jsyk/x65/doc/pic/aura-on-pcb.jpg

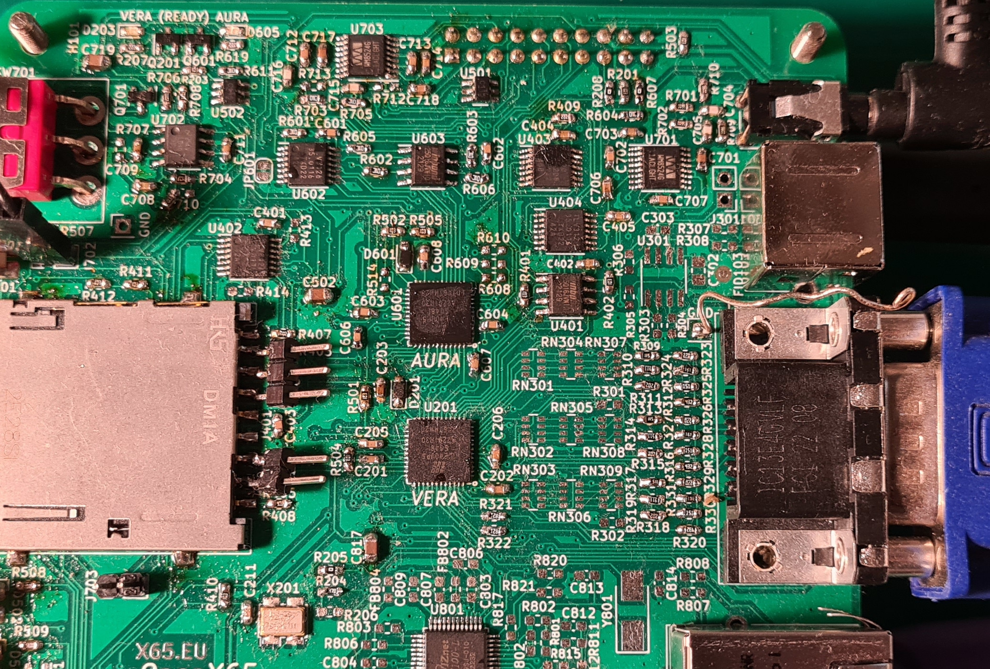
doc/pic/aura-on-pcb.jpg
