jsyk/x65/doc/pic/icd-random-trace-with-regread.png

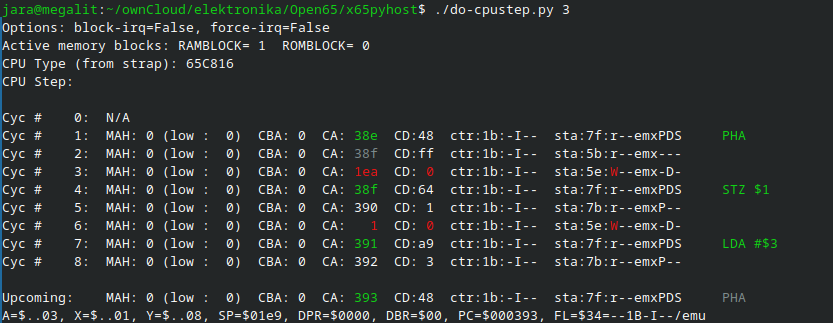
doc/pic/icd-random-trace-with-regread.png
