jsyk/x65/doc/pic/icd-regread-16bit-mx.png

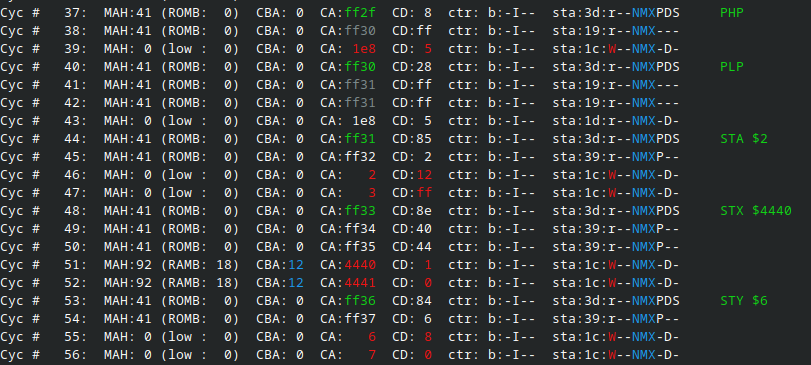
doc/pic/icd-regread-16bit-mx.png
