jsyk/x65/doc/pic/icd-regread-sta-stx-sty-bra.png

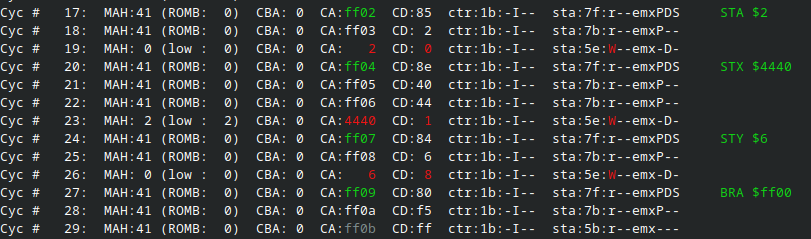
doc/pic/icd-regread-sta-stx-sty-bra.png
