jsyk/x65/doc/pic/of816-welcome.png

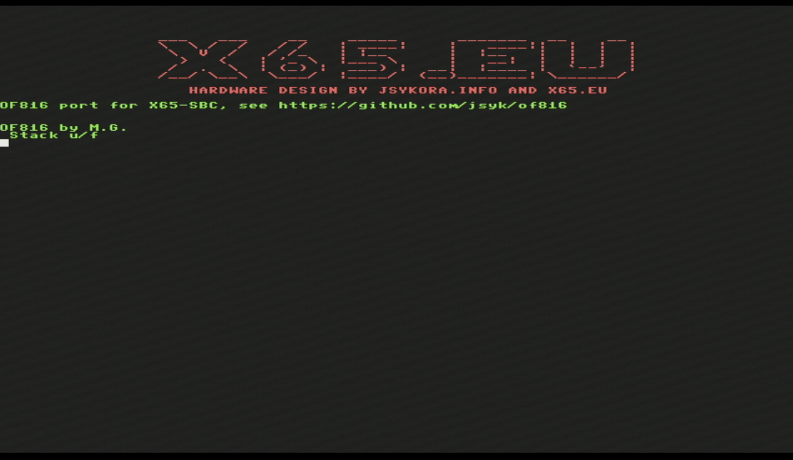
doc/pic/of816-welcome.png
