jsyk/x65/pcb/productions/2023-04-28--PCBWay-vabo-rev01/pcbdata2fab/Screenshot_20230428_151026.png

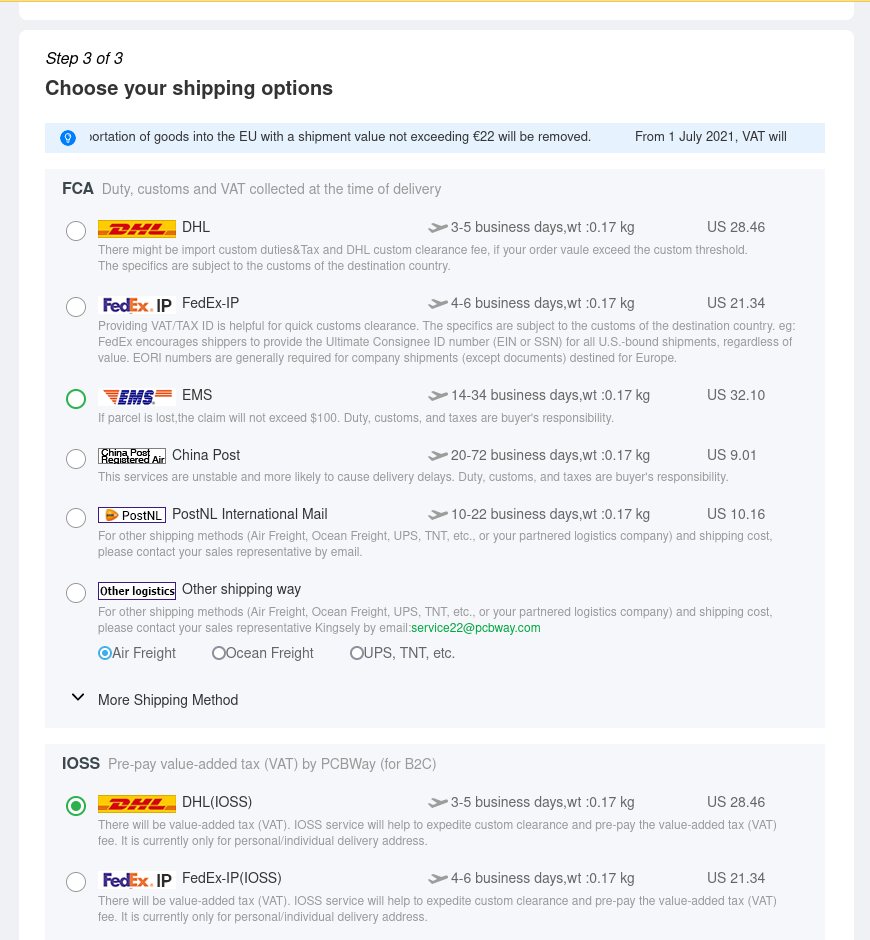
pcb/productions/2023-04-28--PCBWay-vabo-rev01/pcbdata2fab/Screenshot_20230428_151026.png
