jsyk/x65/pcb/productions/2024-01-14--JLCPCB-sbc-revA1/pcbdata2fab/Screenshot_20240114_134323.png

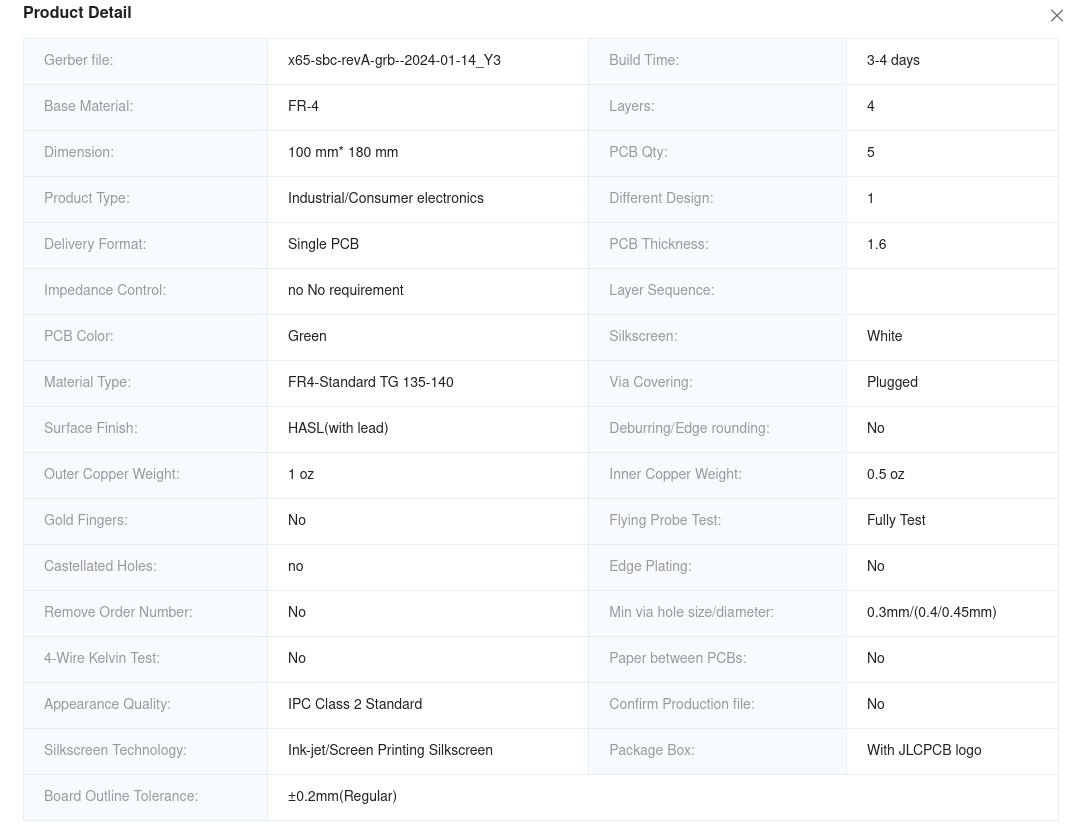
pcb/productions/2024-01-14--JLCPCB-sbc-revA1/pcbdata2fab/Screenshot_20240114_134323.png
