jsyk/x65/pcb/x65-sbc-revB1/pictures/1503_07_LUMBERG.jpg

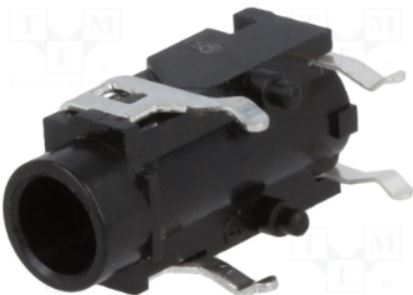
pcb/x65-sbc-revB1/pictures/1503_07_LUMBERG.jpg
