jsyk/x65/pcb/x65-sbc-revB1/pictures/DM1AA-SF-PEJ(82).jpg

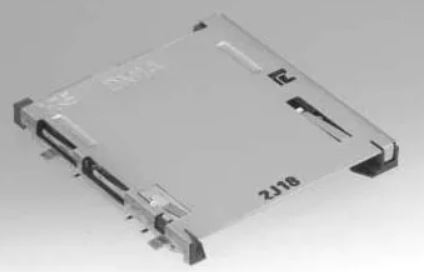
pcb/x65-sbc-revB1/pictures/DM1AA-SF-PEJ(82).jpg
