jsyk/x65/pcb/x65-sbc-revB1/pictures/DS1013-10RSIB-CONNFLY.jpg

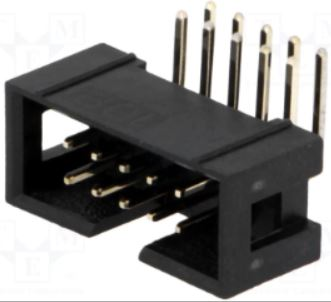
pcb/x65-sbc-revB1/pictures/DS1013-10RSIB-CONNFLY.jpg
