jsyk/x65/pcb/x65-sbc-revB1/pictures/ICD15S13E4GV00LF.jpg

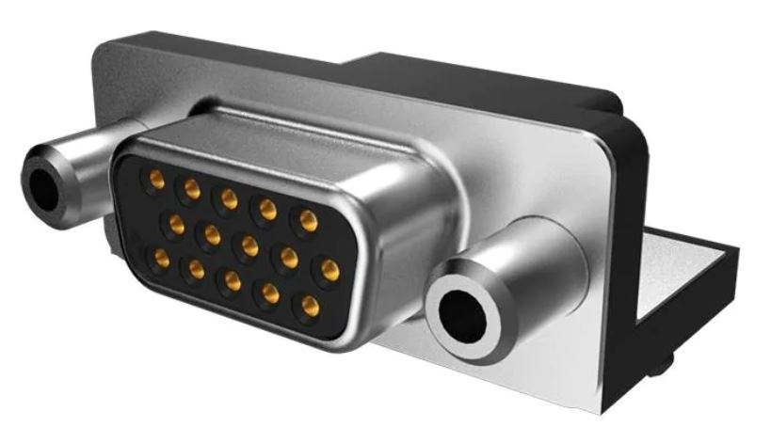
pcb/x65-sbc-revB1/pictures/ICD15S13E4GV00LF.jpg
