jsyk/x65/pcb/x65-sbc-revB1/pictures/idc2x10p.jpg

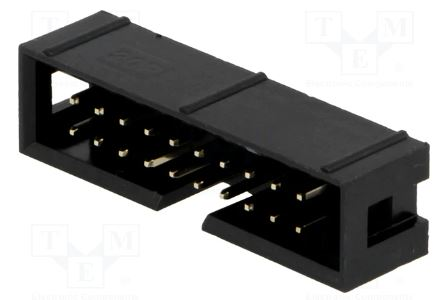
pcb/x65-sbc-revB1/pictures/idc2x10p.jpg
