jsyk/x65/pcb/x65-sbc-revB1/pictures/JC-128.jpg

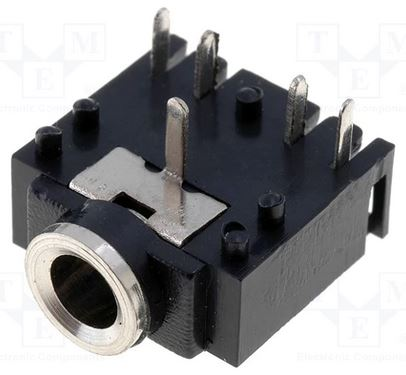
pcb/x65-sbc-revB1/pictures/JC-128.jpg
