jsyk/x65/pcb/x65-sbc-revB1/pictures/ps2minidin6.jpg

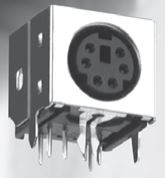
pcb/x65-sbc-revB1/pictures/ps2minidin6.jpg
