jsyk/x65/pcb/x65-sbc-revB1/pictures/R0141-2-10K_SR_PASSIVES.jpg

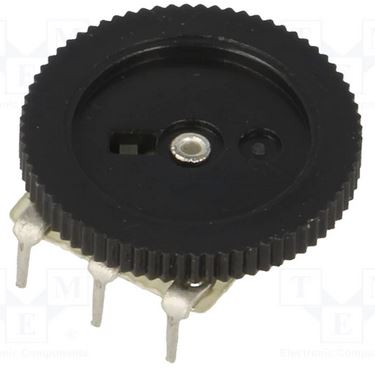
pcb/x65-sbc-revB1/pictures/R0141-2-10K_SR_PASSIVES.jpg
