jsyk/x65/pcb/x65-sbc-revB1/pictures/reflectorled.jpg

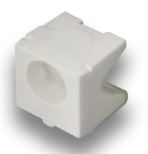
pcb/x65-sbc-revB1/pictures/reflectorled.jpg
