jsyk/x65/pcb/x65-sbc-revB1/pictures/RJMG1BD3B8K1ANR.jpg

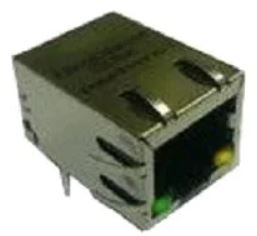
pcb/x65-sbc-revB1/pictures/RJMG1BD3B8K1ANR.jpg
