jsyk/x65/pcb/x65-sbc-revB1/pictures/snes-controller.jpg

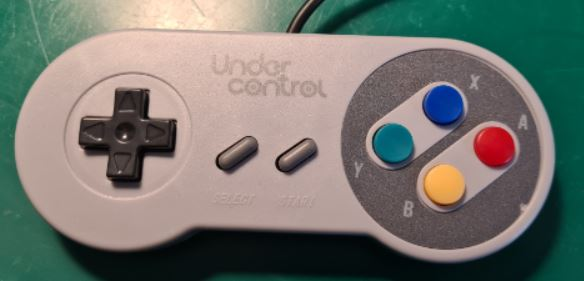
pcb/x65-sbc-revB1/pictures/snes-controller.jpg
