jsyk/x65/pcb/x65-sbc-revB1/pictures/snes_photo_pin1.png

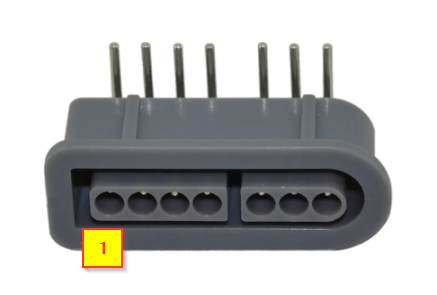
pcb/x65-sbc-revB1/pictures/snes_photo_pin1.png
