jsyk/x65/pcb/x65-sbc-revB1/pictures/usb4085.png

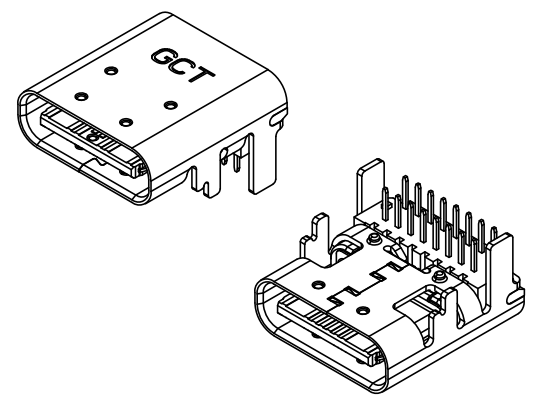
pcb/x65-sbc-revB1/pictures/usb4085.png
