jsyk/x65/Photos/20230507_213943-bitmaptest.jpg

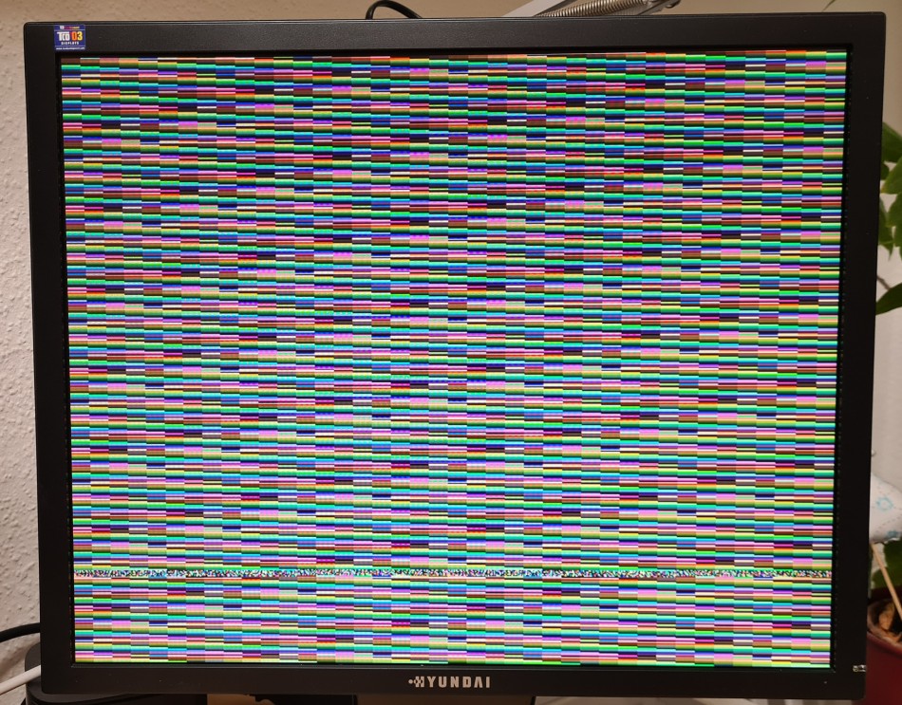
Photos/20230507_213943-bitmaptest.jpg
