jsyk/x65/Photos/20230507_221308-chartest.jpg

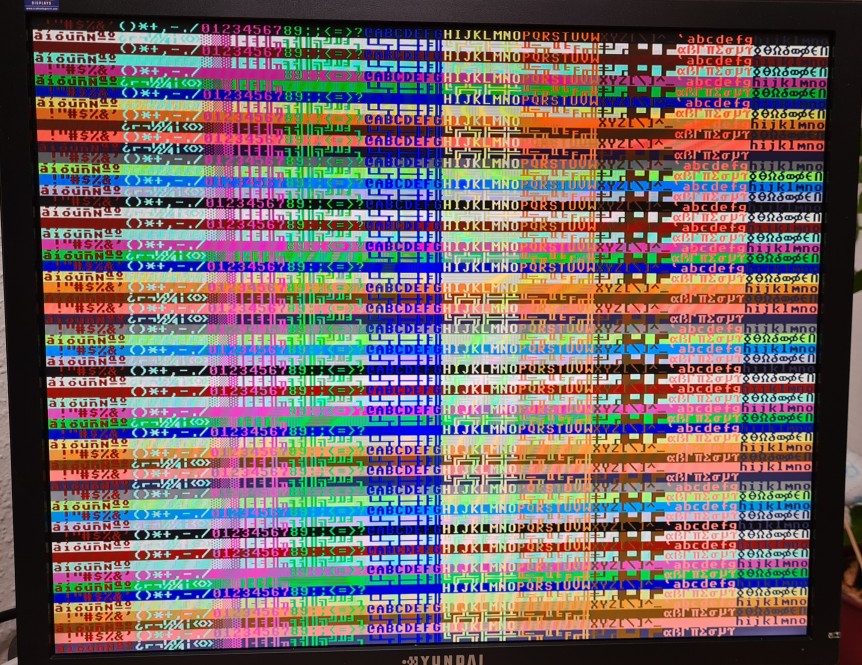
Photos/20230507_221308-chartest.jpg
