jsyk/x65/Photos/20230507_222250-chartest.jpg

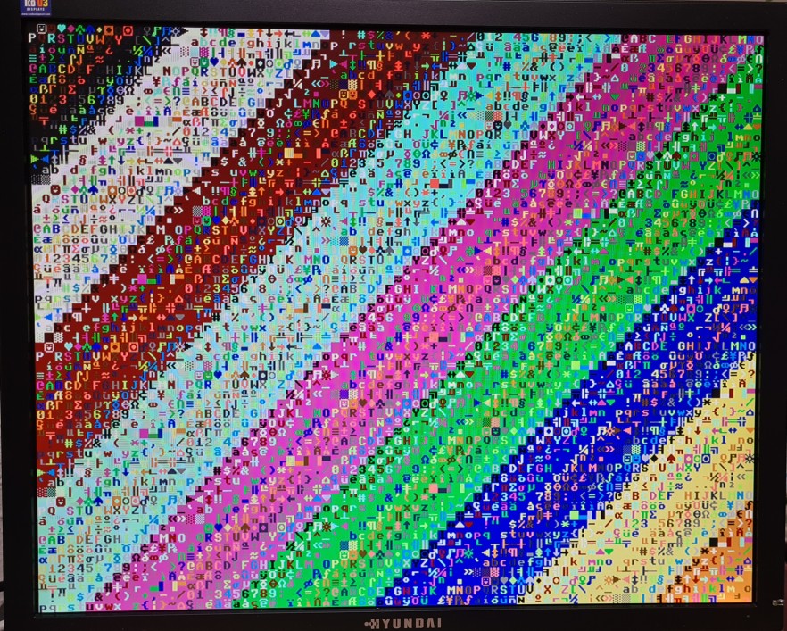
Photos/20230507_222250-chartest.jpg
