jsyk/x65/Photos/20230508_200637-topview.jpg

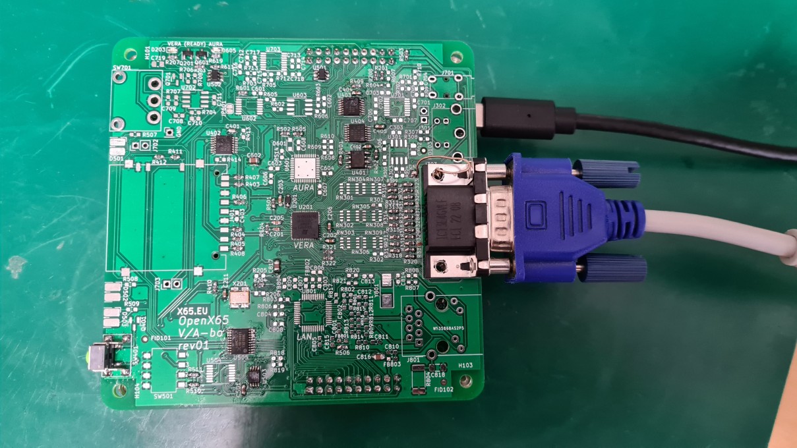
Photos/20230508_200637-topview.jpg
