jsyk/x65/Photos/20230508_200652-frontview.jpg

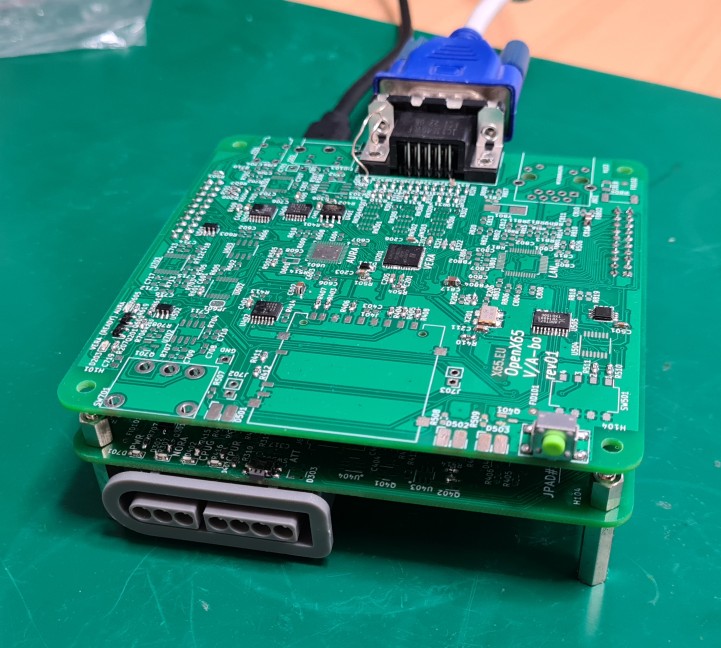
Photos/20230508_200652-frontview.jpg
