jsyk/x65/Photos/20230508_200711-backview.jpg

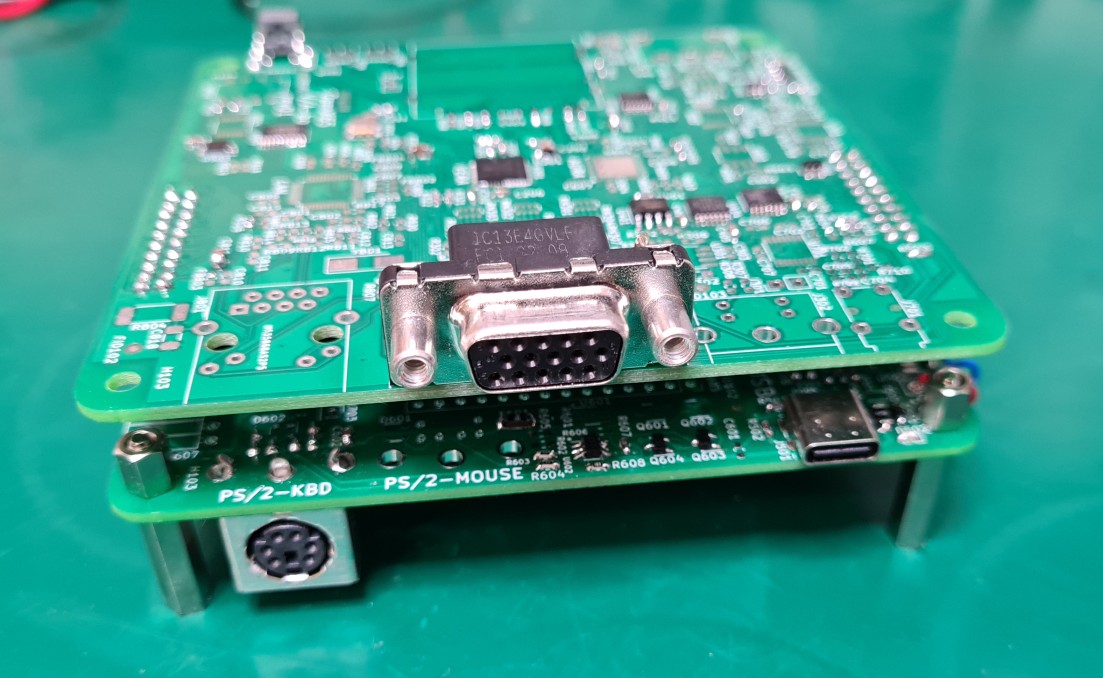
Photos/20230508_200711-backview.jpg
