jsyk/x65/Photos/20230508_200722-vabo-top.jpg

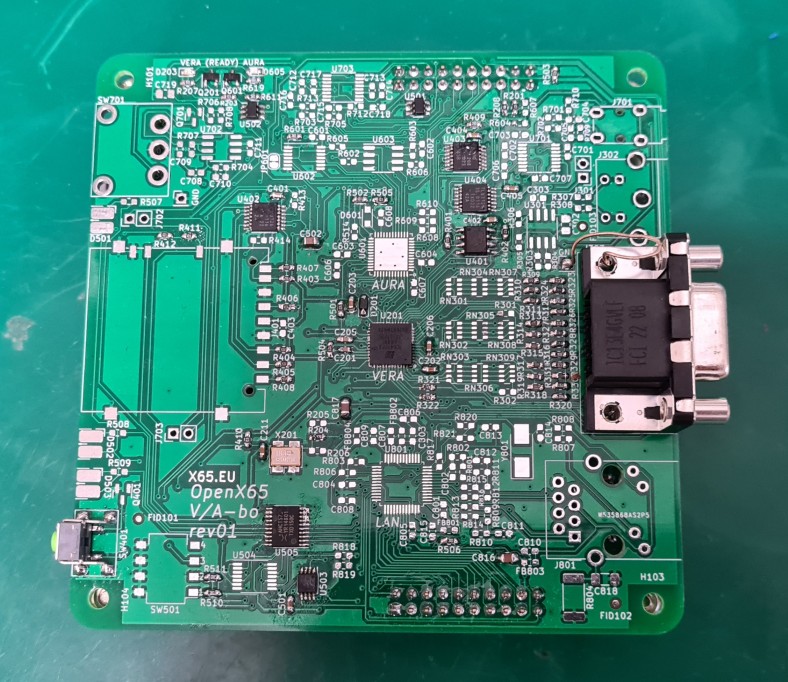
Photos/20230508_200722-vabo-top.jpg
