jsyk/x65/Photos/20230508_200750-mobo-top.jpg

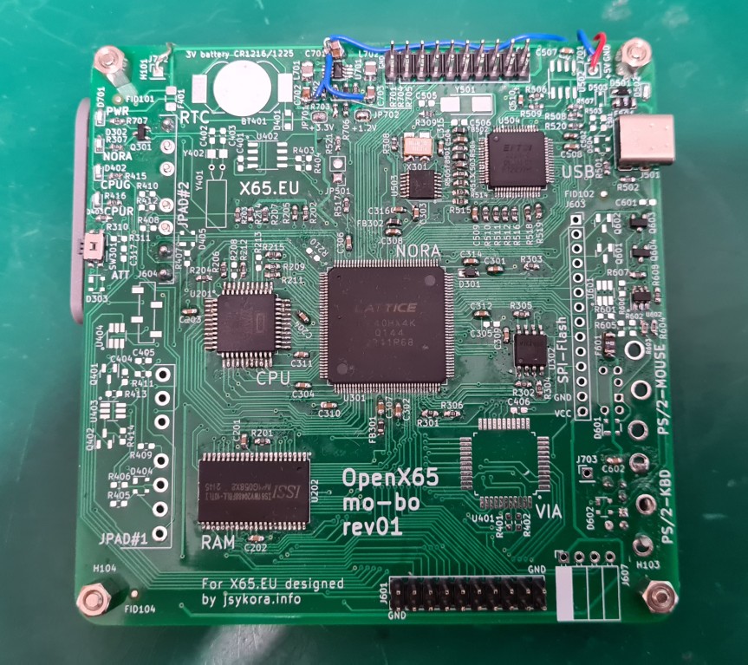
Photos/20230508_200750-mobo-top.jpg
