jsyk/x65/Photos/20230514_201322-mazeprog.jpg

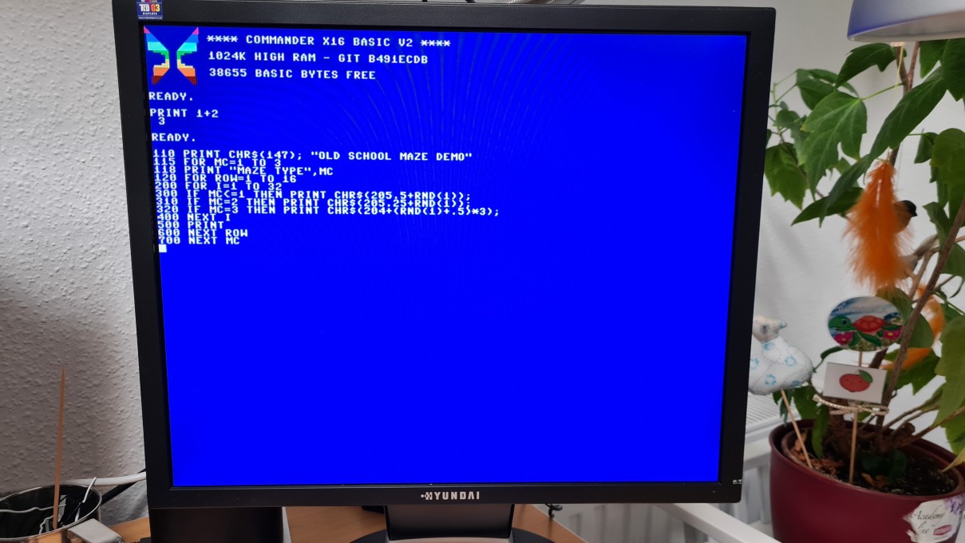
Photos/20230514_201322-mazeprog.jpg
