jsyk/x65/Photos/20230514_201336-mazerun.jpg

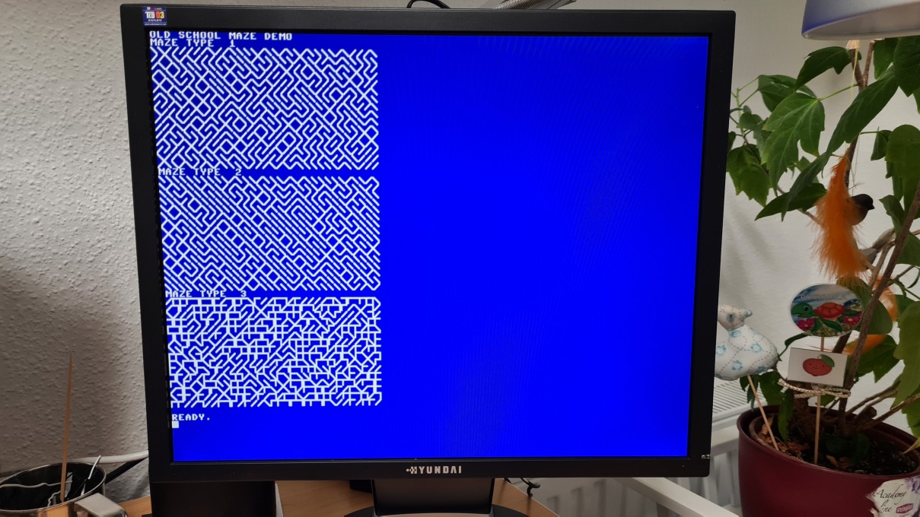
Photos/20230514_201336-mazerun.jpg
