jsyk/x65/Photos/20231208_170810-vabo-top.jpg

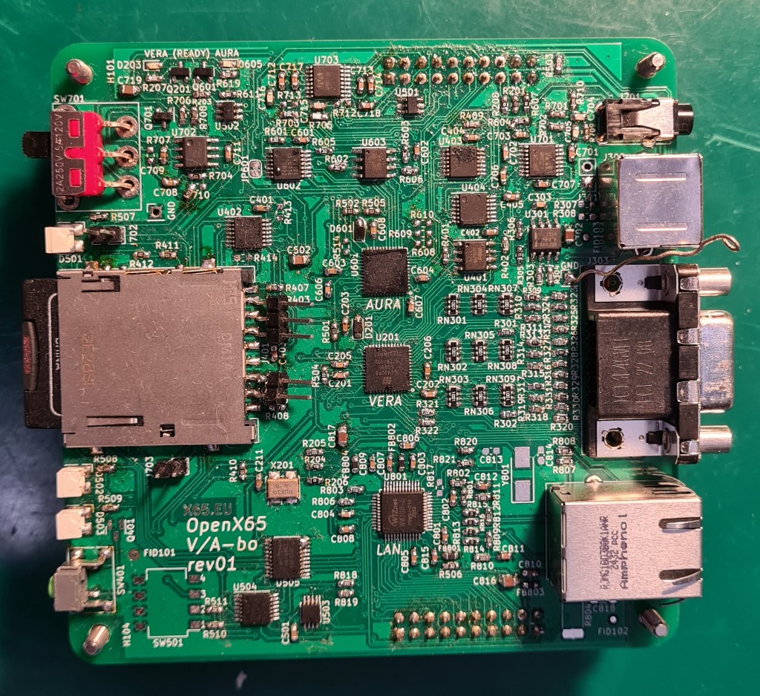
Photos/20231208_170810-vabo-top.jpg
