jsyk/x65/Photos/20231208_170908-mobo-top.jpg

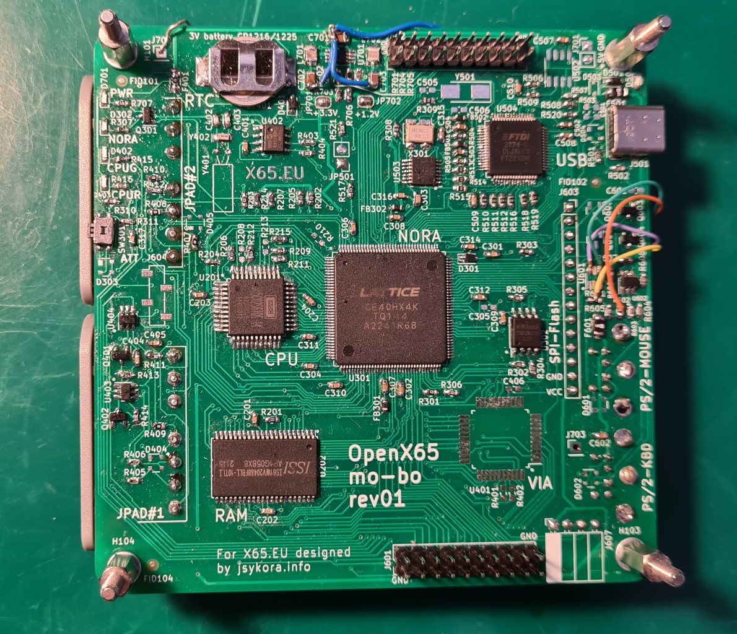
Photos/20231208_170908-mobo-top.jpg
