jsyk/x65/Photos/frontview.jpg

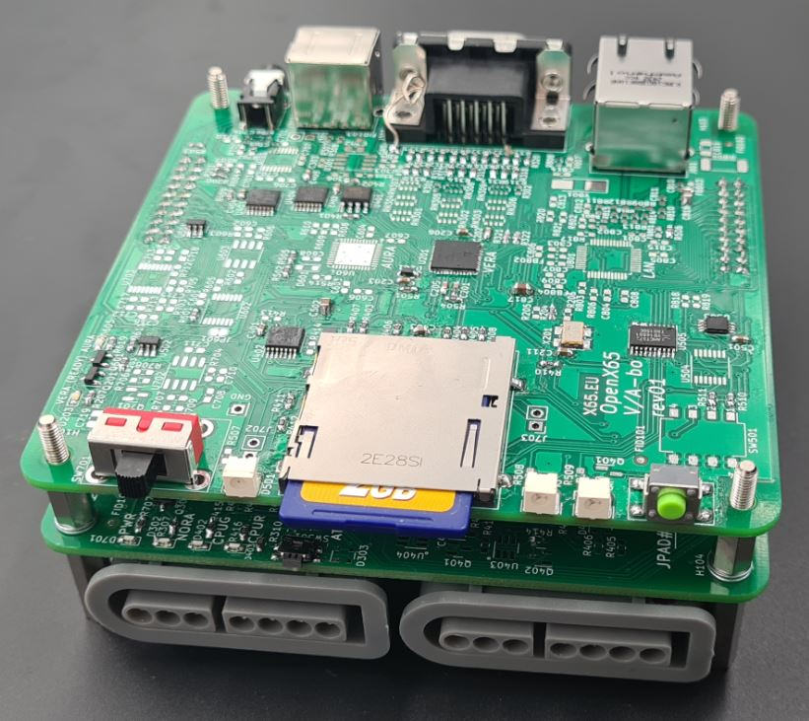
Photos/frontview.jpg
