jsyk/x65/Photos/rearview.jpg

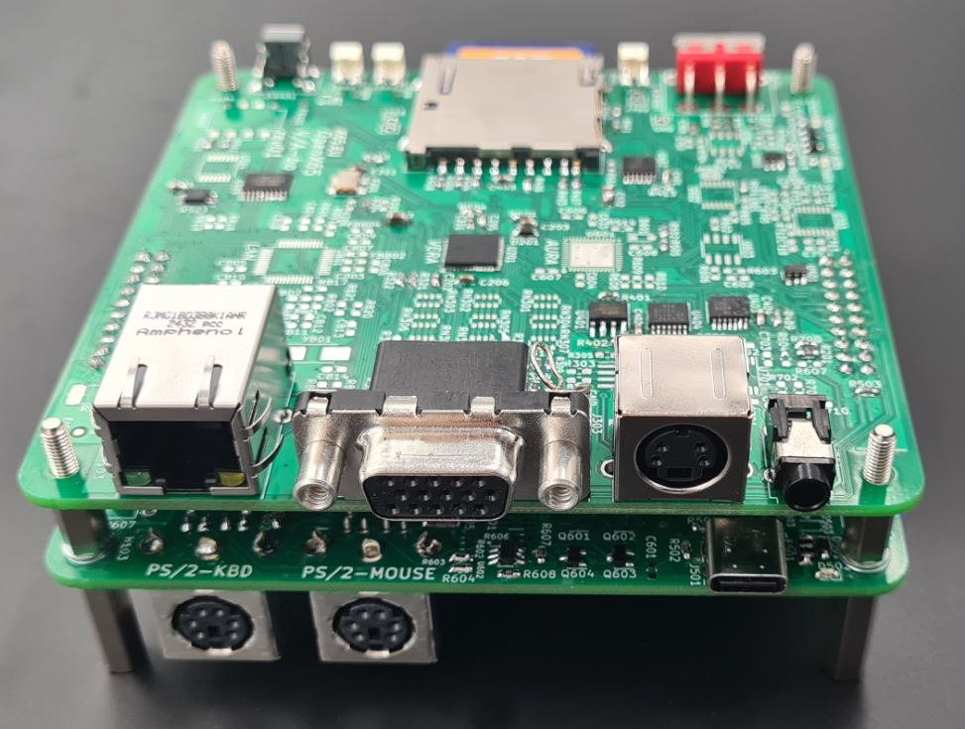
Photos/rearview.jpg
