jsyk/x65/Photos/sbc-topview.jpg

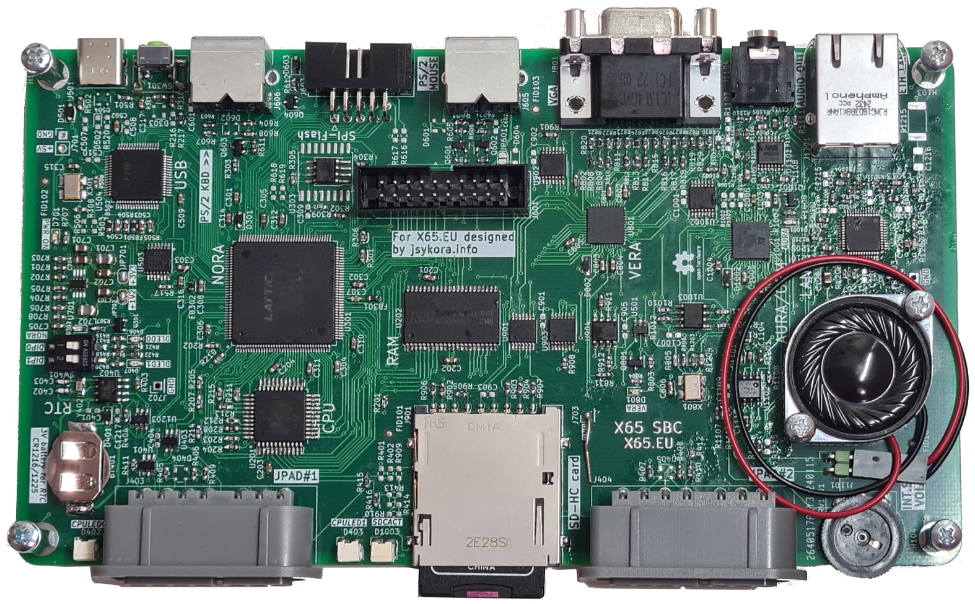
Photos/sbc-topview.jpg
