jsyk/x65/web/6502alive.png

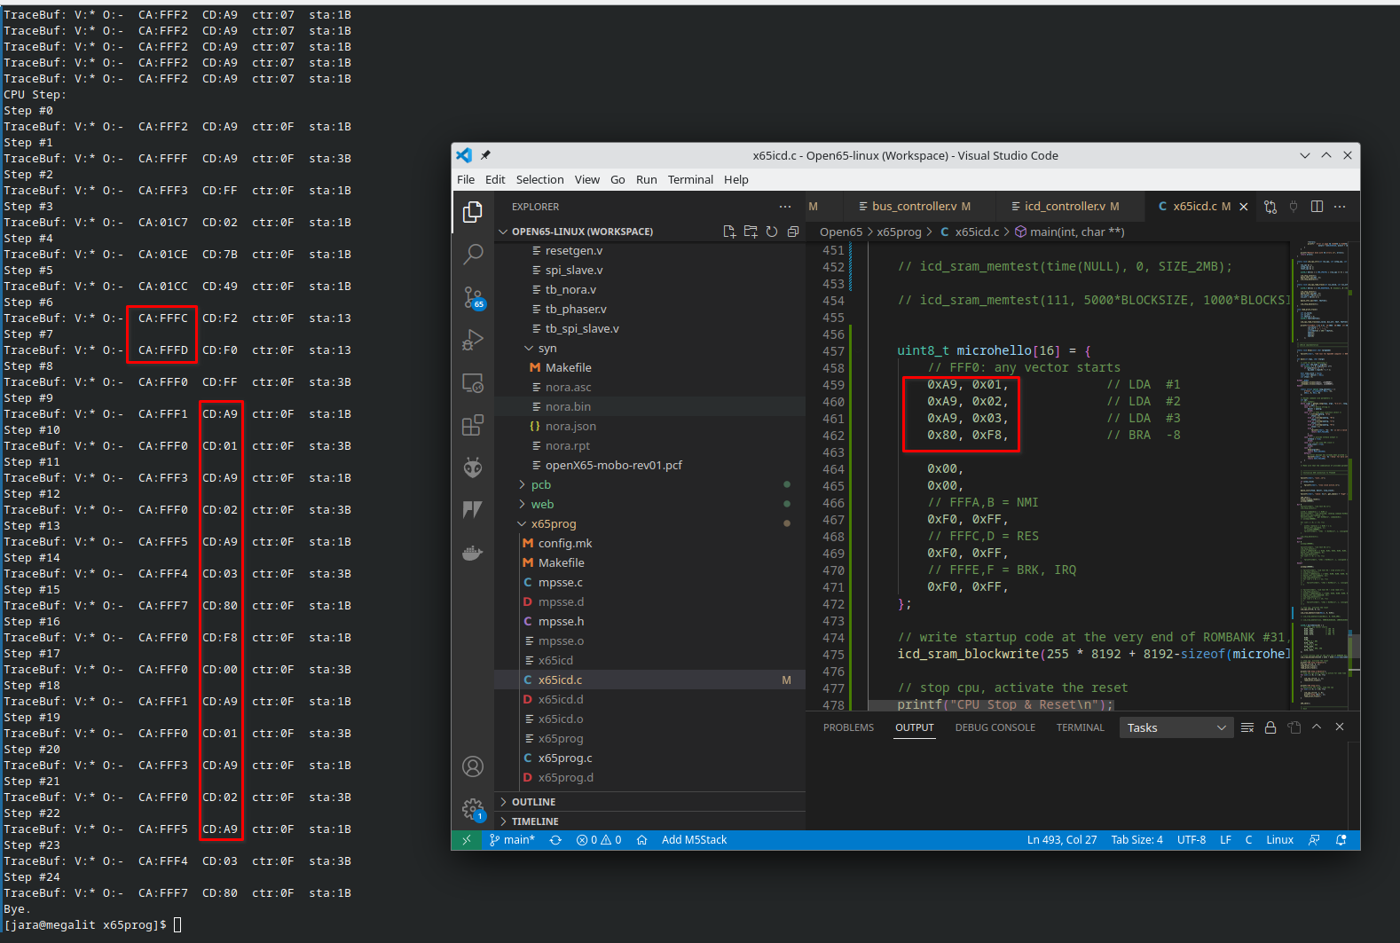
web/6502alive.png
