jsyk/x65/web/bwpcb.png

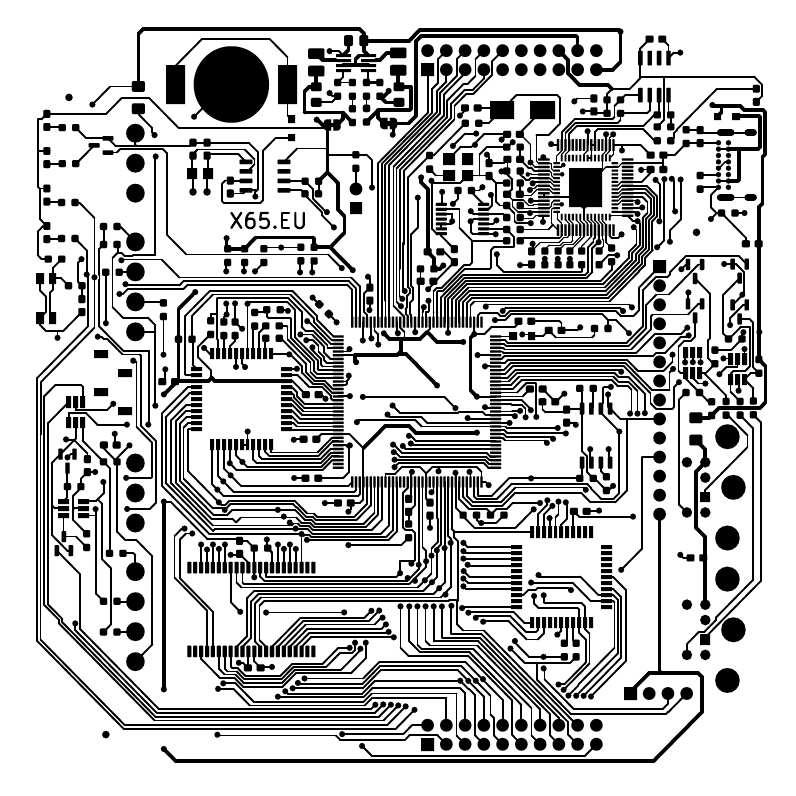
web/bwpcb.png
