jsyk/x65/web/openx65-blockdiagram.png

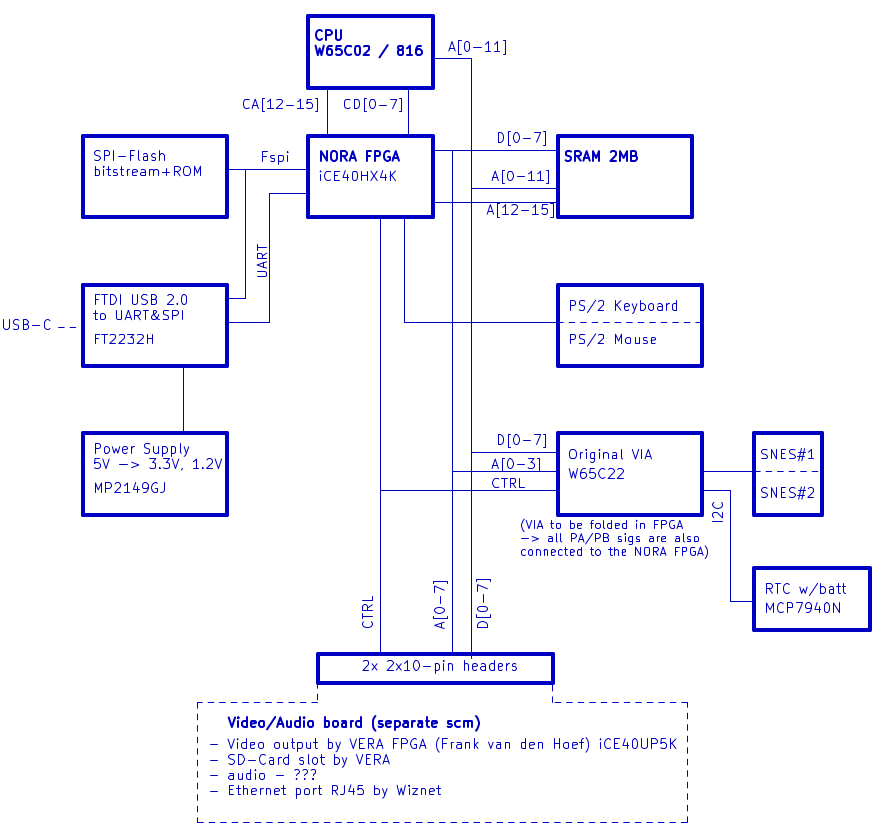
web/openx65-blockdiagram.png
