jsyk/x65/x65pyhost/Windows-LibUsb-Zadig.png

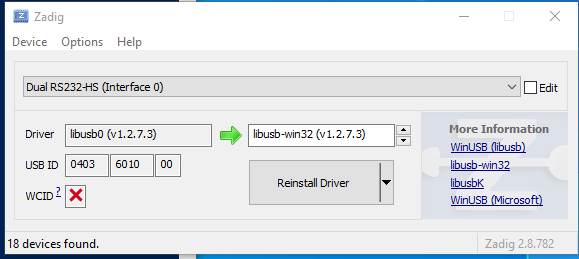
x65pyhost/Windows-LibUsb-Zadig.png
