jsyk/x65/Address Space.ods

Sheet: CPU-MEM
CPU Address Space 65C02 / 65C816 – common first 64kB
CPU has 64kB = 8 * 8kB pages
Addr start | Addr end | Count [B] | CPU Page(8k) | CX16 ? | OpenX65 ? | Description | Allocated to
0x0000 | 0x0000 | 1 | 0 | Y | Y | Current RAM-page (0-255) | NORA
0x0001 | 0x0001 | 1 | 0 | Y | Y | Current ROM-page (0-31) | NORA
0x0002 | 0x0021 | 32 | 0 | Y | Y | 16 bit ABI registers r0-r15 for KERNAL API | SRAM
0x0022 | 0x007F | 94 | 0 | Y | Y | User zero page | SRAM
0x0080 | 0x00FF | 128 | 0 | Y | Y | KERNAL and BASIC zero page variables | SRAM
0x0100 | 0x01FF | 256 | 0 | Y | Y | Accumulator stack | SRAM
0x0200 | 0x03FF | 512 | 0 | Y | Y | KERNAL and BASIC variables, vectors | SRAM
0x0400 | 0x07FF | 1024 | 0 | Y | Y | User space | SRAM
0x0800 | 0x1FFF | 38656 | 0 | Y | Y | BASIC program/variable RAM | SRAM
0x2000 | 0x9EFF | 38656 | 1-4 | Y | Y | BASIC program/variable RAM | SRAM
0x9F00 | 0x9F0F | 16 | 4 | Y | Y | VIA I/O controller #1 | VIA
0x9F10 | 0x9F1F | 16 | 4 | Y | N | VIA I/O controller #2 | reserved
0x9F20 | 0x9F3F | 32 | 4 | Y | Y | VERA video controller | VERA
0x9F40 | 0x9F41 | 2 | 4 | Y | N | YM2151 audio controller | AURA
0x9F42 | 0x9F4F | 14 | 4 | reserved | reserved | reserved | reserved
0x9F50 | 0x9F5F | 16 | 4 | reserved | Y | NORA SCRB FPGA | NORA
0x9F60 | 0x9F6F
0x9F80 | 0x9F8F | 16 | 4 | reserved | Y | W6100 ethernet | W6100
0x9F90 | 0x9FFF | 144 | 4 |  |  | external devices | reserved
0xA000 | 0xBFFF | 8192 | 5 | Y | Y | RAM Bank window (CX16: 512K total, expandable to 2MB; OpenX65: 1496 kB ??) | SRAM
0xC000 | 0xFFFF | 16384 | 6-7 | Y | Y | ROM Bank window (512K total) = 32 rom-banks a 16kB | SRAM

Sheet: SRAM-2MB
SRAM 2MB (21-bits)
SRAM has 2048kB = 256 * 8kB pages
SRAM Page start | SRAM Page end | Page count | SRAM start | SRAM end | kBytes | Description
0 | 63 | 64 | 0x0 | 0x7FFFF | 512 | Low memory – fix-mapped at 65C02 CPU pages 0-4
64 | 127 | 64 | 0x80000 | 0xFFFFF | 512 | ROM pages: 32x, each 16kB, mapped to CPU pages 6-7 according to REG01 – ROMPAGE
128 | 255 | 128 | 0x100000 | 0x1FFFFF | 1024 | High memory – mapped to CPU page 5 according to REG00 – RAMPAGE; RAMPAGE > 127 wraps around to the SRAM page 0

Sheet: SRAM-MAP
SRAM 2MB to CPU Mapping (Unwrapped)
SRAM has 2048kB = 256 * 8kB pages
SRAM 8kB-Page # | SRAM start | SRAM end | CPU 65C02 Mapping | CPU 65C816 Mapping | RAM-PAGE Index @($A0000) | ROM-PAGE Index @($C0000)
0 | 0x000000 | 0x001FFF | $0000 to $1FFF | 0x000000 to 0x001FFF | RAM PAGE 128
1 | 0x002000 | 0x003FFF | $2000 to $3FFF | 0x002000 to 0x003FFF | RAM PAGE 129
2 | 0x004000 | 0x005FFF | $4000 to $5FFF | 0x004000 to 0x005FFF | RAM PAGE 130
3 | 0x006000 | 0x007FFF | $6000 to $7FFF | 0x006000 to 0x007FFF | RAM PAGE 131
4 | 0x008000 | 0x009FFF | $8000 to $9FFF | 0x008000 to 0x009FFF | RAM PAGE 132
5 | 0x00A000 | 0x00BFFF |  |  | RAM PAGE 133
6 | 0x00C000 | 0x00DFFF |  |  | RAM PAGE 134
7 | 0x00E000 | 0x00FFFF |  |  | RAM PAGE 135
8 | 0x010000 | 0x011FFF |  | 0x010000 to 0x011FFF | RAM PAGE 136
9 | 0x012000 | 0x013FFF |  | 0x012000 to 0x013FFF | RAM PAGE 137
10 | 0x014000 | 0x015FFF |  | 0x014000 to 0x015FFF | RAM PAGE 138
11 | 0x016000 | 0x017FFF |  | 0x016000 to 0x017FFF | RAM PAGE 139
12 | 0x018000 | 0x019FFF |  | 0x018000 to 0x019FFF | RAM PAGE 140
13 | 0x01A000 | 0x01BFFF |  | 0x01A000 to 0x01BFFF | RAM PAGE 141
14 | 0x01C000 | 0x01DFFF |  | 0x01C000 to 0x01DFFF | RAM PAGE 142
15 | 0x01E000 | 0x01FFFF |  | 0x01E000 to 0x01FFFF | RAM PAGE 143
16 | 0x020000 | 0x021FFF |  | 0x020000 to 0x021FFF | RAM PAGE 144
17 | 0x022000 | 0x023FFF |  | 0x022000 to 0x023FFF | RAM PAGE 145
18 | 0x024000 | 0x025FFF |  | 0x024000 to 0x025FFF | RAM PAGE 146
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
245 | 0x1EA000 | 0x1EBFFF |  | 0x1EA000 to 0x1EBFFF | RAM PAGE 117
246 | 0x1EC000 | 0x1EDFFF |  | 0x1EC000 to 0x1EDFFF | RAM PAGE 118
247 | 0x1EE000 | 0x1EFFFF |  | 0x1EE000 to 0x1EFFFF | RAM PAGE 119
248 | 0x1F0000 | 0x1F1FFF |  | 0x1F0000 to 0x1F1FFF | RAM PAGE 120
249 | 0x1F2000 | 0x1F3FFF |  | 0x1F2000 to 0x1F3FFF | RAM PAGE 121
250 | 0x1F4000 | 0x1F5FFF |  | 0x1F4000 to 0x1F5FFF | RAM PAGE 122
251 | 0x1F6000 | 0x1F7FFF |  | 0x1F6000 to 0x1F7FFF | RAM PAGE 123
252 | 0x1F8000 | 0x1F9FFF |  | 0x1F8000 to 0x1F9FFF | RAM PAGE 124
253 | 0x1FA000 | 0x1FBFFF |  | 0x1FA000 to 0x1FBFFF | RAM PAGE 125
254 | 0x1FC000 | 0x1FDFFF |  | 0x1FC000 to 0x1FDFFF | RAM PAGE 126
255 | 0x1FE000 | 0x1FFFFF |  | 0x1FE000 to 0x1FFFFF | RAM PAGE 127

Sheet: I2C SMC
SMC over I2C
The system management controller (SMC) is device $42 on the I2C bus. It controls the power and activity LEDs, and can be used to power down the system or inject RESET and NMI signals.
Register | Value | Description – CX16 | Description – X65
0x01 | 0x00 | Power Off | ignored
0x01 | 0x01 | Hard reboot | TBD yes
0x02 | 0x00 | Inject RESET | TBD yes
0x03 | 0x00 | Inject NMI | TBD yes
0x04 | 00..FF | Power LED brightness | ignored
0x05 | 00..FF | Activity LED brightness | ignored
0x07 |  | Read from keyboard buffer | TBD yes
0x18 |  | Read ps2 (keyboard) status | TBD yes
0x19 | 00..FF | Send ps2 command | TBD yes
0x21 |  | Read from mouse buffer | TBD yes

Sheet: IO AREA
IO AREA 256B from CPU:0x9F00 to 0x9FFF
Addr | Module
0x9F0_ | VIA1
0x9F1_ | VIA2 | not implemented
0x9F2_ to 0x9F3_ | VERA
0x9F4_ | AURA
0x9F5_ | NORA
0x9F6_
0x9F7_
0x9F8_ | ENET WIZNET
0x9F9_

Sheet: NORA REGS
NORA
Addr | Module | Reg name | Bit | Read Function | Write Function
0x9F50 | NORA | RAMBANK_MASK_REG | [7:0] | read RAMBANK_MASK_REG | write RAMBANK_MASK_REG
0x9F51 | NORA | RESET_REG |  | tbd | tbd
0x9F52 | NORA | SPI_CTRLSTAT_REG |  | read SPI_STAT | write SPI_CTRL | see spi_host.v for register description
0x9F53 | NORA | SPI_DATA_REG | [7:0] | read from SPI data FIFO | write to SPI data FIFO
0x9F54 | NORA | UART_CTRLSTAT_REG
0x9F55 | NORA | UART_DATA_REG
 | NORA ID | NORA_ID |  | Read NORA ID / version | (write ignored)
 | PS2 KBD | PS2K_BUF |  | Read from keyboard buffer FIFO | Send PS2 command or value (just 1B buffer)
 | PS2 KBD | PS2K_STAT |  | Read PS2 kbd status | Clear PS2 kbd status
 |  | [0] |  | Bit: Port Busy (RX/TX ongoing)
 |  | [1] |  | Bit: Buffer FIFO is non-empty
 |  | [2] |  | Bit: Buffer FIFO has overflown
 |  | [3] |  | Bit: Error on RX (parity)
 |  | [4] |  | Bit: error on TX (missing ACK)
 |  | [5] |  | Bit: TX finished OK (ACK ok)
 |  | [6] |  | Bit: reserved
 |  | [7] |  | Bit: Interrupt Enable
 | PS2 MOUSE | PS2M_BUF |  | Read from mouse buffer FIFO | Send PS2 command or value (just 1B buffer)
 | PS2 MOUSE | PS2M_STAT |  | Read PS2 mouse status | Clear PS2 mouse status
 | I2C MST | 2B?
 | UART_UEXT | 2B
 | UART_FTDI | 2B
 | IRQ | 1B |  | sources: kbd, mouse, uart rx/tx,
 | NMI | 1B
 | SMC | ??

Sheet: VIA REGS
Simple VIA 1
Addr | Module | Reg name | Read Function | Write Function
0x9F00 | VIA1 | REG_ORB_IRB | Input register B | Output register 'B'
0x9F01 | VIA1 | REG_ORA_IRA | Input register A | Output register 'A'
0x9F02 | VIA1 | REG_DDRB | Data direction register B | ..=
0x9F03 | VIA1 | REG_DDRA | Data direction register A | ..=
0x9F04 | VIA1 | REG_T1CL | T1 low-order counter | T1 Low-order latches
0x9F05 | VIA1 | REG_T1CH | T1 high-order counter | ..=
0x9F06 | VIA1 | REG_T1LL | T1 low-order latches | ..=
0x9F07 | VIA1 | REG_T1LH | T1 high-order latches | ..=
0x9F08 | VIA1 | REG_T2CL | T2 low-order counter | T2 low-order latches
0x9F09 | VIA1 | REG_T2CH | T2 high-order counter | ..=
0x9F0A | VIA1 | REG_SR | Shift register | ..=
0x9F0B | VIA1 | REG_ACR | Aux control register | ..=
0x9F0C | VIA1 | REG_PCR | Peripheral control register | ..=
0x9F0D | VIA1 | REG_IFR | Interrupt flag register | ..= | HACKED!! to always return 0x20
0x9F0E | VIA1 | REG_IER | Interrupt enable register | ..=
0x9F0F | VIA1 | REG_ORA_IRA_NOHS | Same as reg 1 except no handshake

Sheet: AURA REGS
AURA
Addr | Module | Reg name | Bit | Read Function | Write Function
0x9F40 | IKAOPM | ADDR_REG | [7:0] |  | Write to ADDR REG
0x9F41 | IKAOPM | DATA_REG | [7:0] | STATUS REG | Write to DATA REG
0x9F42 | IKAOPM
0x9F43 | IKAOPM
0x9F44
0x9F45
0x9F46
0x9F47
0x9F48
0x9F49
0x9F4A
0x9F4B
0x9F4C | IOCS | IOREG | [7:0]
 |  |  | [0] | /SD_CD | /LED0 (active low)
 |  |  | [1] | SD_WP | /LED1 (active low)
 |  |  | [2] | DIP2 | /LED2 (active low)
 |  |  | [3] | DIP1 | /ERST (active low)
0x9F4D | IOCS | IOREG
0x9F4E | IOCS | IOREG
0x9F4F | IOCS | IOREG

Sheet: WIZNET
Ethernet Wiznet
Addr | Module | Reg name | Bit | Read Function | Write Function
0x9F80 | ENET | IDM_ARH |  |  |  | Indirect Mode High address byte
0x9F81 | ENET | IDM_ARL |  |  |  | Indirect Mode Low address byte
0x9F82 | ENET | IDM_BSR |  |  |  | Indirect Mode Block select
0x9F83 | ENET | IDM_DR |  | Data | Data | Data register
