jsyk/x65/pcb/productions/2023-03-29--PCBWay-mobo-rev01/testing/2023-12-21--psu noise 3v3-rev01.png

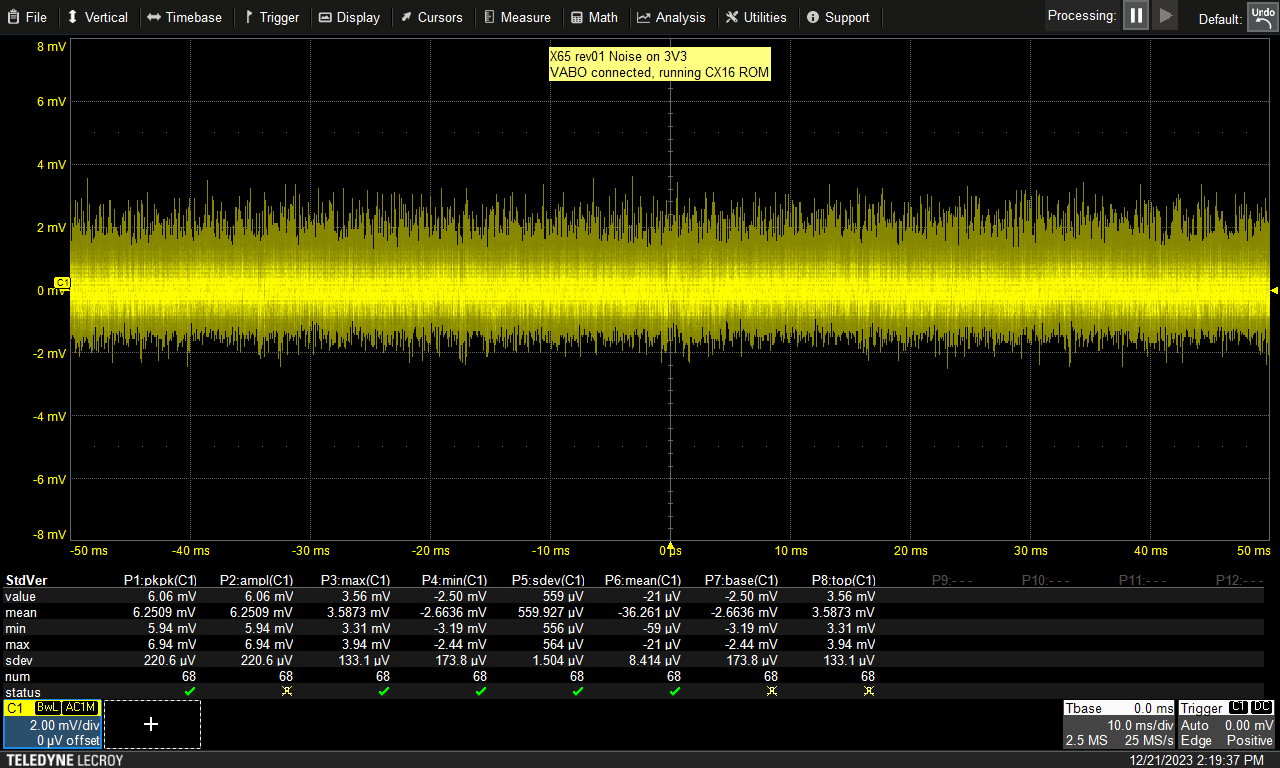
pcb/productions/2023-03-29--PCBWay-mobo-rev01/testing/2023-12-21--psu noise 3v3-rev01.png
