jsyk/x65/pcb/productions/2023-03-29--PCBWay-mobo-rev01/testing/2023-12-25--CPU Data bus vs FPGA, D7, RWB, PHI2, write-to-read complete cycle.png

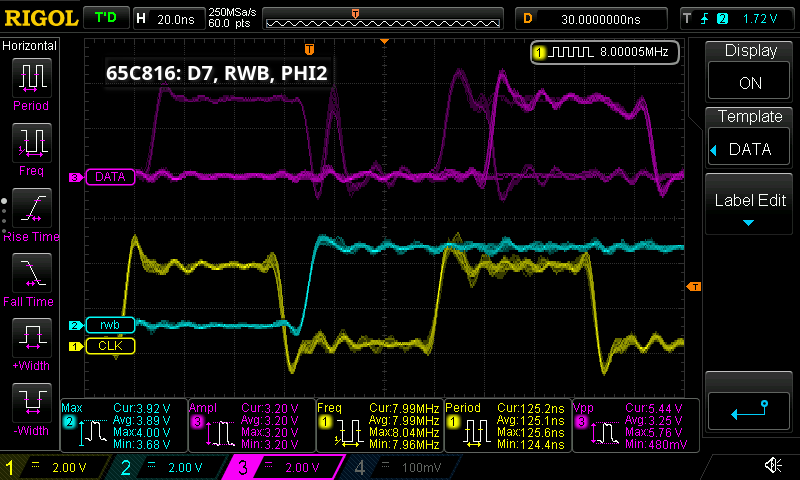
pcb/productions/2023-03-29--PCBWay-mobo-rev01/testing/2023-12-25--CPU Data bus vs FPGA, D7, RWB, PHI2, write-to-read complete cycle.png
