jsyk/x65/pcb/productions/2023-03-29--PCBWay-mobo-rev01/testing/bus phi2 mwrn m-d6 FAIL.png

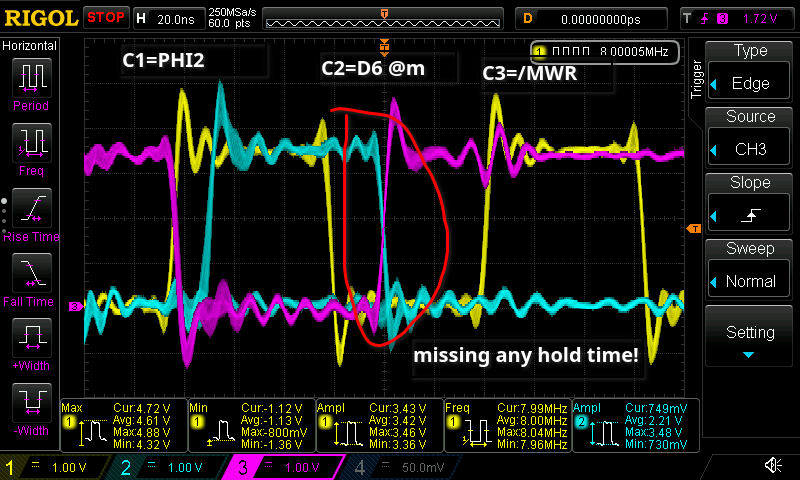
pcb/productions/2023-03-29--PCBWay-mobo-rev01/testing/bus phi2 mwrn m-d6 FAIL.png
