jsyk/x65/pcb/productions/2023-03-29--PCBWay-mobo-rev01/testing/psu seq original-rev01.png

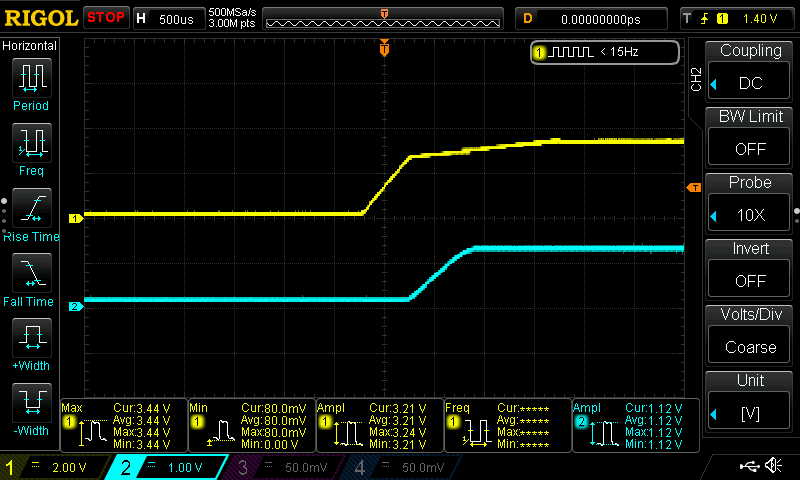
pcb/productions/2023-03-29--PCBWay-mobo-rev01/testing/psu seq original-rev01.png
