jsyk/x65/pcb/productions/2024-01-14--JLCPCB-sbc-revA1/testing/2024-03-08--FTDI ICD_SCK.png

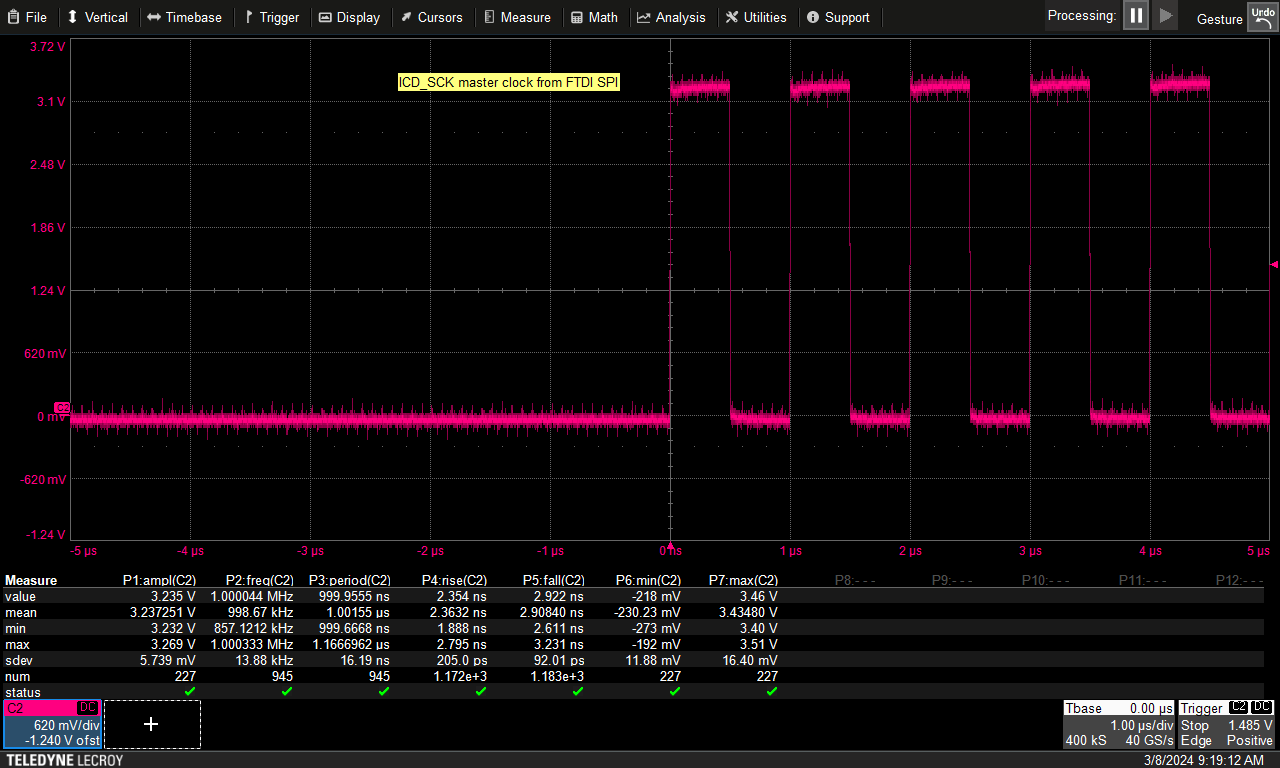
pcb/productions/2024-01-14--JLCPCB-sbc-revA1/testing/2024-03-08--FTDI ICD_SCK.png
