jsyk/x65/pcb/productions/2024-01-14--JLCPCB-sbc-revA1/testing/DS1104Z_2024-01-28_13.59.10__SBC 65C816 writes to VERA.png

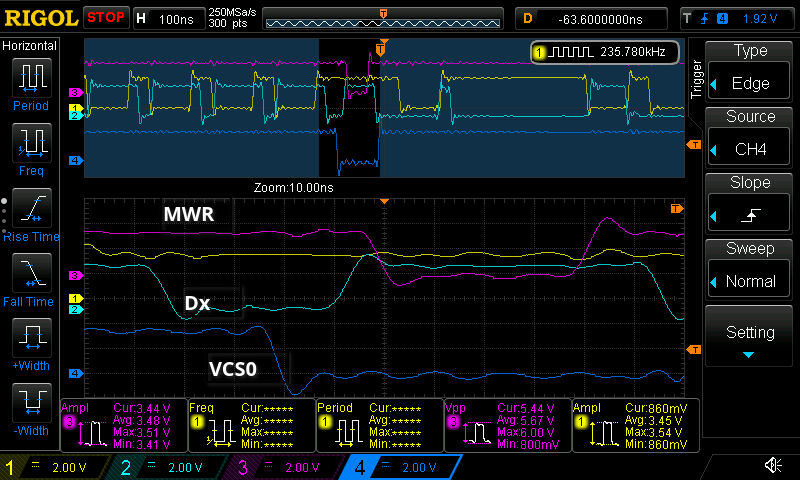
pcb/productions/2024-01-14--JLCPCB-sbc-revA1/testing/DS1104Z_2024-01-28_13.59.10__SBC 65C816 writes to VERA.png
