jsyk/x65/pcb/productions/2024-01-14--JLCPCB-sbc-revA1/testing/DS1104Z_DS1ZA190400748_2024-02-12_18.04.00__SBC Noise on 3V3.png

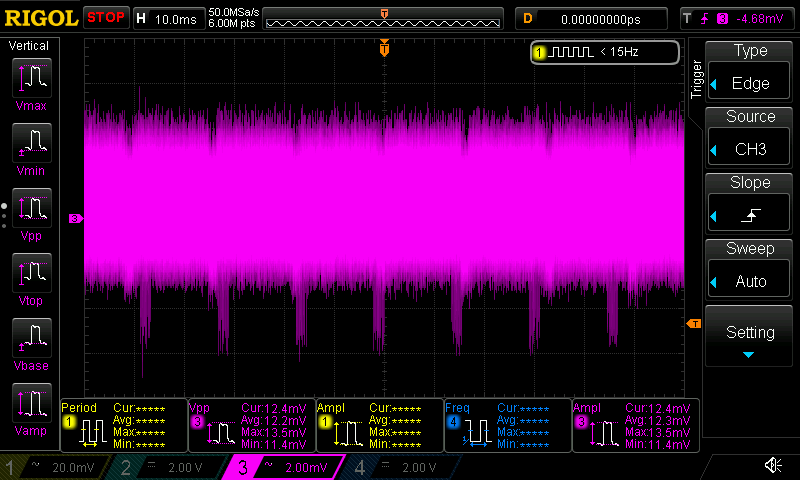
pcb/productions/2024-01-14--JLCPCB-sbc-revA1/testing/DS1104Z_DS1ZA190400748_2024-02-12_18.04.00__SBC Noise on 3V3.png
