jsyk/x65/pcb/productions/2024-01-14--JLCPCB-sbc-revA1/testing/DS1104Z_DS1ZA190400748_2024-03-07_21.47.03__FTDI SPI.png

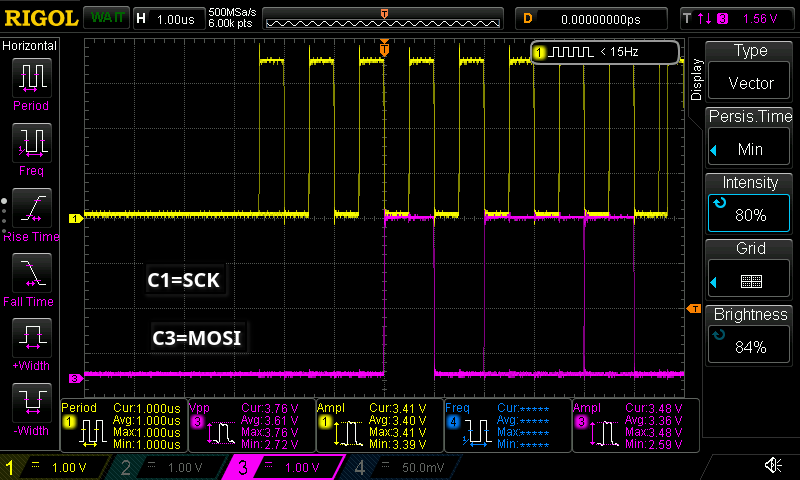
pcb/productions/2024-01-14--JLCPCB-sbc-revA1/testing/DS1104Z_DS1ZA190400748_2024-03-07_21.47.03__FTDI SPI.png
