jsyk/x65/testsw/memtest-c-llvmmos/20231226--memtest-overnight.jpg

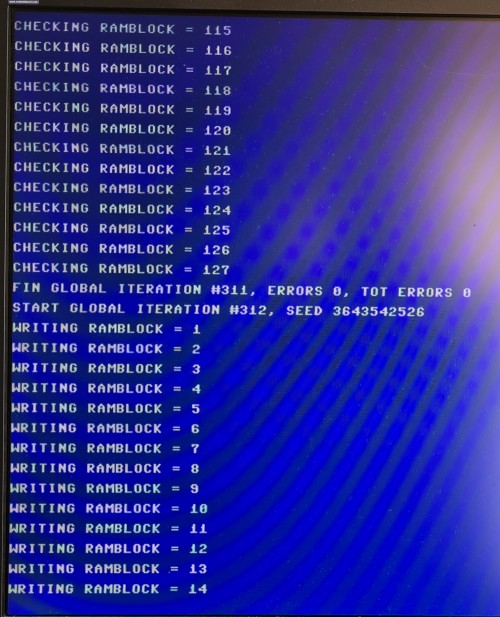
testsw/memtest-c-llvmmos/20231226--memtest-overnight.jpg
