jsyk/x65/fpga-nora/src/tb_nora.v

`timescale 1ns/100ps

module tb_nora ();

`define assert(signal, value) \
        if (signal !== value) begin \
            $display("ASSERTION FAILED in %m: signal != value"); \
            $finish; \
        end

    reg FPGACLK;

// CPU interface
    // reg [15:12] CA;       // CPU address bus
    reg [15:0] cpuCA;
    reg [7:0]  cpuCD;

// SRAM interface
    reg [7:0] sramMD;

    wire CRESn;           // CPU reset
    wire CIRQn;           // CPU IRQ request
    wire CNMIn;           // CPU NMI request
    wire CABORTn;         // CPU ABORT request (16b only)
    wire CPHI2;           // CPU clock
    wire CBE;             // CPU bus-enable

    wire CRDY = 1;             // CPU ready signal
    wire CSOB_MX = 1;          // CPU SOB (set overflow - 8b) / MX (16b)

    reg CSYNC_VPA;        // CPU SYNC (8b) / VPA (16b) signal
    wire CMLn = 1;             // CPU memory lock
    wire CVPn = 1;             // CPU vector pull signal
    wire CVDA = 1;             // CPU VDA (16b only)
    wire CEF = 1;              // CPU EF (16b only)
    reg CRWn;             // CPU R/W signal

    wire [7:0] CD = (CBE && !CRWn) ? cpuCD : 8'hZZ;         // CPU data bus

// Memory bus
    wire [20:12] MAH;      // memory address high bits 12-20: private to FPGA = output
    wire [11:0] MAL = (CBE) ? cpuCA[11:0] : 12'hZZZ;      // memory address low bits 0-11: shared with CPU = bidi
    wire [7:0] MD = (!M1CSn && !MRDn) ? sramMD : 8'hZZ;         // Memory data bus
    wire M1CSn;           // SRAM chip-select
    wire MRDn;            // Memory Read
    wire MWRn;            // Memory Write

    wire CPULED0;
    wire CPULED1;

    wire PS2K_CLK = 1'bZ;
    wire PS2K_DATA = 1'bZ;

    wire PS2M_CLK = 1'bZ;
    wire PS2M_DATA = 1'bZ;

    wire VCS0n_VERA;
    wire VCS1n_AIO;
    wire VCS2n_ENET;

    wire AUDIO_DATA;          // was: VAUX0
    wire AUDIO_BCK;           // was: VAUX1
    wire AUDIO_LRCK;         // was: VAUX2

    wire ICD_CSn = 1'b1;
    wire ICD_MOSI = 1'b1;
    wire ICD_MISO = 1'b1;
    wire ICD_SCK = 1'b1;

// Master SPI interface for SPI-flash access
    wire FMOSI;
    wire FMISO = ~FMOSI;
    wire FSCK;
    wire FLASHCSn;

    reg  ATTBTN;

    reg USBUART_CTS;
    wire USBUART_RTS;
    wire USBUART_TX;
    wire USBUART_RX = USBUART_TX;

    wire CPUTYPE02 = 1'b1;



    top dut0 (
    // 12MHz FPGA clock input
        .FPGACLK (FPGACLK),

    // CPU interface
        .CD (CD),         // CPU data bus
        .CA (cpuCA[15:12]),       // CPU address bus

        .CRESn (CRESn),           // CPU reset
        .CIRQn (CIRQn),           // CPU IRQ request
        .CNMIn (CNMIn),           // CPU NMI request
        .CABORTn (CABORTn),         // CPU ABORT request (16b only)
        .CPHI2 (CPHI2),           // CPU clock
        .CBE (CBE),             // CPU bus-enable

        .CRDY (CRDY),             // CPU ready signal
        .CSOB_MX (CSOB_MX),          // CPU SOB (set overflow - 8b) / MX (16b)

        .CSYNC_VPA (CSYNC_VPA),        // CPU SYNC (8b) / VPA (16b) signal
        .CMLn (CMLn),             // CPU memory lock
        .CVPn (CVPn),             // CPU vector pull signal
        .CVDA (CVDA),             // CPU VDA (16b only)
        .CEF (CEF),              // CPU EF (16b only)
        .CRWn (CRWn),             // CPU R/W signal


    // Memory bus
        .MAH (MAH),      // memory address high bits 12-20: private to FPGA = output
        .MAL (MAL),      // memory address low bits 0-11: shared with CPU = bidi
        .MD (MD),         // Memory data bus
        .M1CSn (M1CSn),           // SRAM chip-select
        .MRDn (MRDn),            // Memory Read
        .MWRn (MWRn),            // Memory Write

    // VIA interface
        // output VIAPHI2,
        // output VIACS,
        // .VIAIRQ (1'b1),
        // output PERIRESn,

        // .I2C_SCL (1'b1),
        // .I2C_SDA (1'b1),

        // .NESLATCH (1'b1),
        // .NESCLOCK (1'b1),
        .NESDATA1 (1'b1),
        .NESDATA0 (1'b1),

        .CPULED0 (CPULED0),
        .CPULED1 (CPULED1),

    // additional ILI SPI ports
        // output ILICSn,
        // output ILIDC,
        // output TCSn,
        
        .CPUTYPE02 (CPUTYPE02),

    // PS2 ports
        .PS2K_CLK (PS2K_CLK),
        .PS2K_DATA (PS2K_DATA),
        // output PS2K_CLKDR,
        // output PS2K_DATADR,
        
        .PS2M_CLK (PS2M_CLK),
        .PS2M_DATA (PS2M_DATA),
        // output PS2M_CLKDR,
        // output PS2M_DATADR,

    // UART port
        .UART_CTS (USBUART_CTS),
        .UART_RTS (USBUART_RTS),
        .UART_TX (USBUART_TX),
        .UART_RX ( USBUART_RX ),

    // VERA FPGA
        // .VERADONE (1'b1),
        // .VERARSTn (1'b1),
        // .VERAFCSn (1'b1),
        // .ICD2VERAROM (1'b1),

        .VCS0n (VCS0n_VERA),
        .ACS1n (VCS1n_AIO),
        .ECS2n (VCS2n_ENET),
        .VIRQn (1'b1),

        // .AUDIO_DATA (AUDIO_DATA),          // was: VAUX0
        // .AUDIO_BCK (AUDIO_BCK),           // was: VAUX1
        // .AUDIO_LRCK (AUDIO_LRCK),          // was: VAUX2

    // ICD SPI-slave interface
        .ICD_CSn (ICD_CSn),
        .ICD_MOSI (ICD_MOSI),
        .ICD_MISO (ICD_MISO),
        .ICD_SCK (ICD_SCK),

    // Button input
        .ATTBTN (ATTBTN),

    // Master SPI interface for SPI-flash access
        .FMOSI (FMOSI),
        .FMISO (FMISO),
        .FSCK (FSCK),
        .FLASHCSn (FLASHCSn)
    );

    // Clock Generator
    initial FPGACLK = 1'b0;
    always #(20)
    begin
        FPGACLK = ~FPGACLK;
    end

    // data that the CPU has read from NORA/SRAM
    reg [7:0] tb_cpuDataRead;

    // generate CPU read transaction
    task cpu_read;
        input [15:0] addr;
        begin
            #40;        // wait tADS=40ns max.
            cpuCA = addr;
            cpuCD = 8'hZZ;
            CRWn = 1'b1;
            CSYNC_VPA = 1'b0;
            @(posedge CPHI2);
            #(60-15);       // tDSR=15ns min before negedge CPHI2
            // tb_cpuDataRead = CD;
            @(negedge CPHI2);
            #10;            // tDHR=10ns max after negedge CPHI2
            tb_cpuDataRead = CD;
        end
    endtask

    // generate CPU write transaction
    task cpu_write;
        input [15:0] addr;
        input [7:0] wdata;
        begin
            #40;        // wait tADS=40ns max.
            cpuCA = addr;
            cpuCD = 8'hXX;
            CRWn = 1'b0;
            CSYNC_VPA = 1'b0;
            @(posedge CPHI2);
            #40;       // tMDS=40ns max after posedge CPHI2
            cpuCD = wdata;
            @(negedge CPHI2);
            cpuCD = #10 16'hXX;
            CRWn = #10 1'b1;
        end
    endtask


    // task IKAOPM_write;
    //     input       [7:0]   i_TARGET_ADDR;
    //     input       [7:0]   i_WRITE_DATA;
    // begin
    //     // read OPM status reg and wait until BUSY flag is 0.
    //     tb_cpuDataRead = 8'hFF;
    //     while (tb_cpuDataRead[7] == 1)
    //     begin
    //         cpu_read(16'h9F40);
    //     end

    //     #2000;
    //     cpu_write(16'h9F40, i_TARGET_ADDR);
    //     #2000;
    //     cpu_write(16'h9F41, i_WRITE_DATA);
    //     #2000;
    // end endtask

    initial
    begin
        // define initial values of inputs to NORA
        cpuCA = 16'hFFFF;
        cpuCD = 8'hZZ;
        // MAL = 12'hFFF;
        // CD = 8'h00;
        // CRDY = 1'b1;
        CRWn = 1'b1;
        // CSOB_MX = 1'b1;
        CSYNC_VPA = 1'b0;
        // ICD_MISO = 1'b1;
        ATTBTN <= 1;
        USBUART_CTS <= 0;

        @(negedge CPHI2);
        @(negedge CPHI2);
        @(posedge CRESn);

        // ============================================
        // test-writes CPU->SRAM
        cpu_write(16'h0010, 8'h12);
        cpu_write(16'h0011, 8'h34);
        cpu_write(16'h0012, 8'h56);
        cpu_write(16'h0013, 8'h78);
        
        // test-reads SRAM->CPU
        cpu_read(16'h0010);  `assert(tb_cpuDataRead, 8'h12);
        cpu_read(16'h0011);  `assert(tb_cpuDataRead, 8'h34);
        cpu_read(16'h0012);  `assert(tb_cpuDataRead, 8'h56);
        cpu_read(16'h0013);  `assert(tb_cpuDataRead, 8'h78);

        // ============================================
        // enable ram/rom-block regs at zero page
        cpu_write(16'h9F53, 8'b0011_0000);

        // ============================================
        // write to bank regs
        cpu_write(16'h0000, 8'hAB);         // RAMBANK
        cpu_write(16'h0001, 8'h0C);         // ROMBANK

        // read from bank regs in the zero page
        cpu_read(16'h0000);  `assert(tb_cpuDataRead, 8'hAB);
        cpu_read(16'h0001);  `assert(tb_cpuDataRead, 8'h0C);

        // read from the same bank regs in the io area
        cpu_read(16'h9F50);  `assert(tb_cpuDataRead, 8'hAB);
        cpu_read(16'h9F51);  `assert(tb_cpuDataRead, 8'h0C);

        // ============================================
        // write to VIA
        cpu_write(16'h9F02, 8'h03);         // VIA1/DDRB [1:0] config to outputs
        cpu_write(16'h9F00, 8'h00);         // VIA1/ORB set to 00
        cpu_read(16'h9F02);     `assert(tb_cpuDataRead, 8'h03);
        cpu_write(16'h9F00, 8'h01);         // VIA1/ORB set to 01
        cpu_write(16'h9F00, 8'h02);         // VIA1/ORB set to 01
        cpu_read(16'h9F00);     `assert(tb_cpuDataRead, (8'hC0 | CPUTYPE02));         // fixed upper signal's levels

        // ============================================
        // write to VERA
        cpu_write(16'h9F20, 8'h12);

        // ============================================
        // go to the BOOTROM
        //cpu_write(16'h0001, 8'hFF);         // ROMBANK PBL
        cpu_write(16'h9F53, 8'b1011_0000);      // RMBCTRL
        // test read from BOOTROM
        cpu_read(16'hFFFC);  `assert(tb_cpuDataRead, 8'h00);
        cpu_read(16'hFFFD);  `assert(tb_cpuDataRead, 8'hFE);
        cpu_read(16'hFE00);  `assert(tb_cpuDataRead, 8'hA2);
        cpu_read(16'hFE01);  `assert(tb_cpuDataRead, 8'hFF);

        // test write to BOOTROM
        cpu_write(16'hFE50, 8'hDE);
        cpu_read(16'hFE00);  `assert(tb_cpuDataRead, 8'hA2);
        cpu_read(16'hFE50);  `assert(tb_cpuDataRead, 8'hDE);


        // ============================================
        // TEST OF SPI-MASTER 
        // activate SPI Master for flash access
        cpu_write(16'h9F63, 8'b00_100_001);     // N_SPI_CTRL  
        cpu_read(16'h9F63);  `assert(tb_cpuDataRead, 8'b00_100_001);
        `assert(FLASHCSn, 0);
        // write data to the SPI master DATA REG for TX
        cpu_write(16'h9F65, 8'h03);     // N_SPI_DATA  
        cpu_write(16'h9F65, 8'h12);  
        cpu_write(16'h9F65, 8'h34);  
        // read SPIM STAT REG and poll until rx/tx is done
        cpu_read(16'h9F64);         // N_SPI_STAT
        while (tb_cpuDataRead[7])   // bit [7] = Is BUSY?
        begin
            cpu_read(16'h9F64);     // N_SPI_STAT
        end
        // read SPI DATA REG to pull out the RX bytes
        cpu_read(16'h9F65);  `assert(tb_cpuDataRead, ~8'h03);
        cpu_read(16'h9F65);  `assert(tb_cpuDataRead, ~8'h12);
        cpu_read(16'h9F65);  `assert(tb_cpuDataRead, ~8'h34);

        // ============================================
        // TEST OF USB-UART INTERFACE

        // read USB_UART_CTRL
        cpu_read(16'h9F55); `assert(tb_cpuDataRead, 8'h04);     // just 115200 Bd
        // read USB_UART_STAT
        cpu_read(16'h9F56); `assert(tb_cpuDataRead, 8'h84);     // RXFifoEmpty, TXfifoempty
        // write USB_UART_CTRL: set 1Mbps speed, so that the TB runs faster.
        cpu_write(16'h9F55, 8'h06);
        // write $9F57           USB_UART_DATA       
        cpu_write(16'h9F57, 8'hA5);
        cpu_write(16'h9F57, 8'hA6);
        cpu_write(16'h9F57, 8'hA7);
        cpu_write(16'h9F57, 8'hA8);
        cpu_write(16'h9F57, 8'hA9);
        cpu_write(16'h9F57, 8'hB0);
        cpu_write(16'h9F57, 8'hB1);
        cpu_write(16'h9F57, 8'hB2);
        cpu_write(16'h9F57, 8'hB3);
        cpu_write(16'h9F57, 8'hB4);
        cpu_write(16'h9F57, 8'hB5);
        cpu_write(16'h9F57, 8'hB6);
        // wait until character is received in the loopback
        cpu_read(16'h9F56);     // USB_UART_STAT
        while (tb_cpuDataRead[7])   // bit [7] = Is RX FIFO empty?
        begin
            cpu_read(16'h9F56);
        end
        // bit is zero -> some char in the buffer
        cpu_read(16'h9F57); `assert(tb_cpuDataRead, 8'hA5);
        
        // wait until TX FIFO is empty - all chars were sent
        cpu_read(16'h9F56);     // USB_UART_STAT
        while (!tb_cpuDataRead[2])   // bit [7] = Is TX FIFO empty?
        begin
            cpu_read(16'h9F56);
        end

        // read USB_UART_STAT
        // cpu_read(16'h9F56); `assert(tb_cpuDataRead, 8'h84);     // RXFifoEmpty, TXfifoempty

        // ============================================
        // TEST OF PS2 REGS
        // read PS2_CTRL, expect 0
        cpu_read(16'h9F5E); `assert(tb_cpuDataRead, 8'h00);
        // write PS2_CTRL
        cpu_write(16'h9F5E, 8'hFF);
        // read PS2_CTRL, expect 11
        cpu_read(16'h9F5E); `assert(tb_cpuDataRead, 8'h03);
        // write to KBD buffer
        cpu_write(16'h9F60, 8'hAA); 


        // ============================================
        // test of IKAOPM
        // KC
        // cpu_write(16'h9F40, 8'h28);
        // cpu_write(16'h9F41, {4'h4, 4'h2});

        //KC
        // #(600*35) IKAOPM_write(8'h28, {4'h4, 4'h2}); //ch1

        // //MUL
        // #(600*35) IKAOPM_write(8'h40, {1'b0, 3'd0, 4'd2}); 
        // #(600*35) IKAOPM_write(8'h50, {1'b0, 3'd0, 4'd1});

        // //TL
        // #(600*35) IKAOPM_write(8'h60, {8'd21});
        // #(600*35) IKAOPM_write(8'h70, {8'd1});
        // #(600*35) IKAOPM_write(8'h68, {8'd127});
        // #(600*35) IKAOPM_write(8'h78, {8'd127});

        // //AR
        // #(600*35) IKAOPM_write(8'h80, {2'd0, 1'b0, 5'd31}); 
        // #(600*35) IKAOPM_write(8'h90, {2'd0, 1'b0, 5'd30});

        // //AMEN/D1R(DR)
        // #(600*35) IKAOPM_write(8'hA0, {1'b0, 2'b00, 5'd5});
        // #(600*35) IKAOPM_write(8'hB0, {1'b0, 2'b00, 5'd18});

        // //D2R(SR)
        // #(600*35) IKAOPM_write(8'hC0, {2'd0, 1'b0, 5'd0});
        // #(600*35) IKAOPM_write(8'hD0, {2'd0, 1'b0, 5'd7});

        // //D1L(SL)RR
        // #(600*35) IKAOPM_write(8'hE0, {4'd0, 4'd0});
        // #(600*35) IKAOPM_write(8'hF0, {4'd1, 4'd4});

        // //RL/FL/ALG
        // #(600*35) IKAOPM_write(8'h20, {2'b11, 3'd7, 3'd4});

        // //KON
        // #(600*35) IKAOPM_write(8'h08, {1'b0, 4'b0011, 3'd0}); //write 0x7F, 0x08(KON)=

        cpu_read(16'h0000);

        #100_000;

        // ============================================
        // ATTBTN <= 0;
        // #100_000;
        // #100_000;
        // #100_000;
        // #100_000_000;

        #1000;
        $display("=== TESTBENCH OK ===");
        $finish;
    end

    // ------------------------------------------------------
    // simulation of SRAM
    reg [7:0] sram_block [255:0];

    // SRAM read
    always @(MRDn, M1CSn)
    begin
        if ((MRDn == 0) && (M1CSn == 0))
        begin
            sramMD <= #20 sram_block[MAL[7:0]];
        end else begin
            sramMD <= 8'hXX;
        end
    end

    // SRAM write
    always @(posedge MWRn)
    begin
        if (M1CSn == 0)
        begin
            sram_block[MAL[7:0]] <= MD;
        end
    end
    // ------------------------------------------------------

    // Do this in your test bench to generate VCD waves
    initial
    begin
        $dumpfile("tb_nora.vcd");
        $dumpvars(0,tb_nora);
    end


endmodule
