jsyk/x65/fpga-nora/src/tb_ps2kbdhost.v

`timescale 1ns/100ps

module tb_ps2kbdhost ();

`define assert(signal, value) \
        if (signal !== value) begin \
            $display("ASSERTION FAILED in %m: signal != value"); \
            $finish; \
        end

    // Global signals
    reg           clk6x;      // 48MHz
    reg           resetn;     // sync reset
    wire           ck1us;      // 1 usec-spaced pulses, 1T long
    reg [6:0]   ck1us_counter;

    // PS2 port signals
    reg           PS2_CLK;        // CLK line state
    reg           PS2_DATA;       // DATA line state
    wire      PS2_CLKDR0;     // 1=>drive zero on CLK, 0=>HiZ
    wire      PS2_DATADR0;    // 1=>drive zero on DATA, 0=>HiZ

    pulser pulser_1us
    (
        .clk6x (clk6x),       // 48MHz
        .resetn (resetn),     // sync reset
        .ck1us (ck1us)
    );

    localparam RXBUF_DEPTH_BITS = 3;

    wire [7:0]    kbd_rdata;      // RX FIFO byte from PS2 keyboard, or 0x00 in case !kbd_rvalid
    wire          kbd_rvalid;     // RX FIFO byte is valid? (= FIFO not empty?)
    wire [RXBUF_DEPTH_BITS:0]    kbd_rcount;       // RX FIFO count of bytes currently
    reg           kbd_rdeq;       // dequeu (consume) RX FIFO; allowed only iff kbd_rvalid==1
    // Keyboard reply status register, values:
    //      0x00 => idle (no transmission started)
    //      0x01 => transmission pending
    //      0xFA => ACK received
    //      0xFE => ERR received
    wire [7:0]    kbd_stat;
    wire          kbd_bat_ok;      // received the BAT OK code (0xAA) from the keyboard
    // Write to keyboard:
    reg [7:0]     kbd_wcmddata;           // byte for TX FIFO to send into PS2 keyboard
    reg           kbd_enq_cmd1;           // enqueu 1Byte command
    reg           kbd_enq_cmd2;           // enqueu 2Byte command+data

    ps2_kbd_host dut (
        // Global signals
        .clk6x (clk6x),      // 48MHz
        .resetn (resetn),     // sync reset
        .ck1us (ck1us),      // 1us pulses
        // Generic Host interface:
        // Read from keyboard buffer (from RX FIFO)
        .kbd_rdata_o (kbd_rdata),      // RX FIFO byte from PS2 keyboard, or 0x00 in case !kbd_rvalid
        .kbd_rvalid_o (kbd_rvalid),     // RX FIFO byte is valid? (= FIFO not empty?)
        .kbd_rcount_o (kbd_rcount),       // RX FIFO count of bytes currently
        .kbd_rdeq_i (kbd_rdeq),       // dequeu (consume) RX FIFO; allowed only iff kbd_rvalid==1
        // Keyboard reply status register, values:
        //      0x00 => idle (no transmission started)
        //      0x01 => transmission pending
        //      0xFA => ACK received
        //      0xFE => ERR received
        .kbd_stat_o (kbd_stat),
        .kbd_bat_ok_o (kbd_bat_ok),      // received the BAT OK code (0xAA) from the keyboard
        // Write to keyboard:
        .kbd_wcmddata_i (kbd_wcmddata),           // byte for TX FIFO to send into PS2 keyboard
        .kbd_enq_cmd1_i (kbd_enq_cmd1),           // enqueu 1Byte command
        .kbd_enq_cmd2_i (kbd_enq_cmd2),           // enqueu 2Byte command+data
        // PS2 Keyboard port - FPGA pins
        .PS2K_CLK (PS2_CLK),
        .PS2K_DATA (PS2_DATA),
        .PS2K_CLKDR (PS2_CLKDR0),         // 1=drive PS2K_CLK to zero (L)
        .PS2K_DATADR (PS2_DATADR0)         // 1=drive PS2K_DATA to zero (L)
    );


    // Clock Generator
    initial clk6x = 1'b0;
    always #(20)
    begin
        clk6x = ~clk6x;
    end

    integer j;
    
    // reg [7:0]   txdata;
    // reg         txparity;


    // simulate sending from PS2 device
    task send;
        input [7:0] txdata;     // the byte to send from device to port
        reg         txparity;
        begin
            txparity = 1'b0;
            
            // START
            #16500 PS2_DATA = 0;
            #16500 PS2_CLK = 0;
            
            #33000 PS2_CLK = 1;

            for (j = 0; j < 8; ++j)
            begin
                // DATA BIT j
                #16500 PS2_DATA = (txdata >> j);
                txparity = txparity ^ (txdata >> j);
                #16500 PS2_CLK = 0;
                
                #33000 PS2_CLK = 1;
            end

            // PARITY
            #16500 PS2_DATA = ~txparity;
            #16500 PS2_CLK = 0;

            #33000 PS2_CLK = 1;

            // STOP
            #16500 PS2_DATA = 1;
            #16500 PS2_CLK = 0;

            #33000 PS2_CLK = 1;
            
        end
    endtask

    // simulate receiving in PS2 device
    task receive;
        begin
            @(negedge PS2_CLKDR0);

            for (j = 0; j < 10; ++j)
            begin
                #33000 PS2_CLK = 0;
                #33000 PS2_CLK = 1;
            end

            // output the ACK=0
            #16500 PS2_DATA = 0;
            #16500 PS2_CLK = 0;
            #33000 PS2_CLK = 1;
            #16500 PS2_DATA = 1;

        end
    endtask

    // task read_smc_reg;
    //     input [7:0]     smc_reg;
    //     begin
    //         devsel <= 1'b1; rw_bit <= 1'b0;     // write
    //         @(posedge clk6x); @(posedge clk6x); @(posedge clk6x);
    //         rxbyte <= smc_reg;
    //         rxbyte_v <= 1'b1;
    //         @(posedge clk6x);
    //         rxbyte_v <= 1'b0;
    //         @(posedge clk6x);
    //         devsel <= 1'b0;                     // restart
    //         @(posedge clk6x); @(posedge clk6x); @(posedge clk6x);
    //         devsel <= 1'b1; rw_bit <= 1'b1;     // read
    //         @(posedge clk6x); @(posedge clk6x); @(posedge clk6x);
    //         txbyte_deq <= 1'b1;
    //         @(posedge clk6x);
    //         txbyte_deq <= 1'b0;
    //         @(posedge clk6x); @(posedge clk6x); @(posedge clk6x);
    //         devsel <= 1'b0;
    //         @(posedge clk6x); @(posedge clk6x); @(posedge clk6x);
    //     end
    // endtask

    // task write_smc_reg_1b;
    //     input [7:0]     smc_reg;
    //     input [7:0]     dataval;
    //     begin
    //         devsel <= 1'b1; rw_bit <= 1'b0;     // write
    //         @(posedge clk6x); @(posedge clk6x); @(posedge clk6x);
    //         rxbyte <= smc_reg;
    //         rxbyte_v <= 1'b1;
    //         @(posedge clk6x);
    //         rxbyte_v <= 1'b0;
    //         @(posedge clk6x);
    //         @(posedge clk6x); @(posedge clk6x); @(posedge clk6x);
    //         rxbyte <= dataval;
    //         rxbyte_v <= 1'b1;
    //         @(posedge clk6x);
    //         rxbyte_v <= 1'b0;
    //         @(posedge clk6x);
    //         @(posedge clk6x); @(posedge clk6x); @(posedge clk6x);
    //         devsel <= 1'b0;
    //         @(posedge clk6x); @(posedge clk6x); @(posedge clk6x);
    //     end
    // endtask

    // task write_smc_reg_2b;
    //     input [7:0]     smc_reg;
    //     input [7:0]     dataval1;
    //     input [7:0]     dataval2;
    //     begin
    //         devsel <= 1'b1; rw_bit <= 1'b0;     // write
    //         @(posedge clk6x); @(posedge clk6x); @(posedge clk6x);
    //         rxbyte <= smc_reg;
    //         rxbyte_v <= 1'b1;
    //         @(posedge clk6x);
    //         rxbyte_v <= 1'b0;
    //         @(posedge clk6x);
    //         @(posedge clk6x); @(posedge clk6x); @(posedge clk6x);
    //         rxbyte <= dataval1;
    //         rxbyte_v <= 1'b1;
    //         @(posedge clk6x);
    //         rxbyte_v <= 1'b0;
    //         @(posedge clk6x);
    //         @(posedge clk6x); @(posedge clk6x); @(posedge clk6x);

    //         rxbyte <= dataval2;
    //         rxbyte_v <= 1'b1;
    //         @(posedge clk6x);
    //         rxbyte_v <= 1'b0;
    //         @(posedge clk6x);
    //         @(posedge clk6x); @(posedge clk6x); @(posedge clk6x);

    //         devsel <= 1'b0;
    //         @(posedge clk6x); @(posedge clk6x); @(posedge clk6x);
    //     end
    // endtask

    task deque_rd;
        begin
            // dequeue
            @(posedge clk6x);
            kbd_rdeq <= 1;
            @(posedge clk6x);
            kbd_rdeq <= 0;
            @(posedge clk6x);
        end
    endtask

    initial
    begin
        PS2_CLK <= 1;
        PS2_DATA <= 1;
        kbd_rdeq <= 0;
        kbd_wcmddata <= 8'h00;
        kbd_enq_cmd1 <= 0;
        kbd_enq_cmd2 <= 0;
        resetn <= 1'b0;
        
        for (j = 0; j < 20; ++j)
        begin
            @(posedge clk6x);
        end

        resetn <= 1'b1;
        for (j = 0; j < 200; ++j)
        begin
            @(posedge clk6x);
        end


        // read_smc_reg(8'h07);        // smc reg addr = 07 = SMCREG_READ_KBD_BUF
        // expected: 00
        `assert(kbd_rdata, 8'h00);
        `assert(kbd_rvalid, 0);

        // simulate keypress on PS2 keyboard -> output scancodes
        send(8'hC7);
        #100000;
        send(8'h7C);

        #100000;

        // read_smc_reg(8'h07);        // smc reg addr = 07 = SMCREG_READ_KBD_BUF
        // expected: C7
        `assert(kbd_rdata, 8'hC7);
        `assert(kbd_rvalid, 1);
        deque_rd();
        `assert(kbd_rvalid, 1);

        #1000;

        // read_smc_reg(8'h07);        // smc reg addr = 07 = SMCREG_READ_KBD_BUF
        // expected 7C
        `assert(kbd_rdata, 8'h7C);
        `assert(kbd_rvalid, 1);
        deque_rd();
        `assert(kbd_rvalid, 0);

        #1000;

        // write_smc_reg_1b(8'h19, 8'hA5);         // smc reg addr 19 = SMCREG_SEND_PS2_KBD_CMD
        @(posedge clk6x);
        kbd_wcmddata <= 8'hA5;
        kbd_enq_cmd1 <= 1;
        @(posedge clk6x);
        kbd_enq_cmd1 <= 0;
        @(posedge clk6x);

        #100000;

        receive();

        #100000;

        // // write_smc_reg_2b(8'h1A, 8'h55, 8'hAA);         // smc reg addr 1A = SMCREG_SEND_PS2_KBD_2BCMD
        @(posedge clk6x);
        kbd_wcmddata <= 8'h55;
        kbd_enq_cmd2 <= 1;
        @(posedge clk6x);
        kbd_enq_cmd2 <= 0;
        @(posedge clk6x);
        
        #1000;

        @(posedge clk6x);
        kbd_wcmddata <= 8'hAA;
        kbd_enq_cmd2 <= 1;
        @(posedge clk6x);
        kbd_enq_cmd2 <= 0;
        @(posedge clk6x);


        #100000;
        receive();          // ps2 keyboard receiving

        send(8'hFA);       // ps2 keyboard replies with OK (FA)  

        receive();

        send(8'hFA);       // ps2 keyboard replies with OK (FA)  

        #100000;


        $finish;
    end


    // Do this in your test bench to generate VCD waves
    initial
    begin
        $dumpfile("tb_ps2kbdhost.vcd");
        $dumpvars(0, tb_ps2kbdhost);
    end

endmodule
